ms0216/hhkb-split/docs/hardware/provisional-values.md

# まだ実測していない値

**推定で埋めた値と、確かめた値が区別できないと、どこがまだ危ないのかが
分からなくなる。** この案件では、タクトスイッチの向きも XIAO のピンピッチも
推定のまま断定し、どちらも利用者に指摘されて初めて誤りだと分かった。

ここは `[暫定]` と書かれた定数の一覧。
[tools/test_constants.py](../../tools/test_constants.py) が
**コードとこの表がずれたら落ちる**ようにしてある。書き漏らしも、
実測して確定したのに残っている行も、どちらも検出される。

---

## 一覧

| 定数 | 現在値 | 何の値か | どうやって確かめるか | 外したときの影響 |
|---|---|---|---|---|
| `CAP_LIFT` | 6.2mm | プレート上面からキーキャップ底面まで（MX ＋ キャップ） | MX スイッチとキーキャップが届いたら測る | **全段のキートップ高さが実機とずれる。** ここから `PLATE_TOP_FRONT` を逆算しているので影響は全体に及ぶ |
| `CAP_H_HOME` | 7.6mm | ホーム段のキーキャップ自体の高さ | 同上 | 同上 |
| `CAP_H_QWERTY` | 9.16mm | **QWERTY 段**のキャップ高さ。上 2 段だけ背の高いものを混ぜる決定（open-gaps #21）による | **実機のキートップ 35.6mm に一致させるのに要る高さを逆算した要求値で、製品の実測ではない。**この高さの MX 用キャップを実際に探し、買ってノギスで測る | 実機のキートップ高さとずれる。`test_our_design_actually_reaches_the_real_keytop_heights` が差を表に出す |
| `CAP_H_NUMBER` | 11.12mm | 同・**数字段** | 同上（実機 40.0mm から逆算） | 同上 |
| `SOCKET_DROP` | 3.2mm | Kailh ホットスワップソケットが基板下へ出る量 | ソケットが届いたらノギスで測る。**データシート（PG151101S11: 板下 1.80）と kiswitch モデル（端子込み 2.01）とは突き合わせ済み**で、3.2 は 1.19mm 保守側（`test_the_socket_box_contains_the_third_party_model`） | 大きすぎればケースが無駄に厚い。小さすぎればソケットがケース床に当たる |
| `PLATE_TO_PCB` | 3.5mm | プレート下面から基板上面までの距離 | MX スイッチが届いたら、プレートに挿して測る | **キートップの高さが実機とずれる。** HHKB 再現の根幹 |
| `BATT_BOX_W` | 16.6mm | 同・短辺（前後） | 同上 | コブの奥行が足りなくなる。ケースの作り直し |
| `BATT_BOX_H` | 16.8mm | 同・高さ | 同上 | 電池室の高さが足りず、傾いた基板を突き上げる |
| `ANTENNA_L` | 3.5mm | XIAO のチップアンテナが占める長さ（USB と反対の端から） | XIAO の実物か、Seeed の基板図で測る。**いまは概数** | アンテナが本体基板の下から出ているかの判定がずれる（open-gaps #23） |
| LED の点灯電流 | **1〜2mA（推定）** | XIAO 基板上の RGB LED 1 色ぶん（直列抵抗込み）。**コードの定数ではない**ので `tools/` の検査対象には無い | 実機で点灯／消灯の差をシャントで測る（Task C4/C5）。**未実測** | **接続中は消灯なので定常状態では効かない**（実機もそうなっている）。効くのは**未接続で放置したとき**で、緑／青の点滅は 50% デューティ。待機 20µA に対し 3 桁大きいので、長く未接続のまま置くと電池を食う。大きければデューティを下げる（open-gaps #43） |
| `USB_SHELL_EXPOSED` | 1.0mm | 完全に挿さった状態で、プラグの樹脂とケース表面の間に**見えている金属の長さ** | 実機に挿して測った（2026-08-09・ケーブル 1 本）。**ケーブルによって違う**ので、手持ちの数本で測り直し、いちばん短いものに合わせる | 短いケーブルが**奥まで挿さらない**（open-gaps #28） |
| `ANTENNA_W` | 3.5mm | XIAO のチップアンテナの幅 | 現物を実測（概数）。**長手の向きが未確定**なので大きいほうを両方に使っている | 子基板の配線をアンテナの真下から外せるかの判定がずれる |
| `USB_PLUG_W` | 12.0mm | **利用者が挿す USB-C ケーブルの、オス側プラグの樹脂の胴体**の幅 | 手持ちのケーブル数本を測った最大値（分解能 1mm の器具・2026-08-09）。**ノギスで測り直す**。買い足したケーブルが太ければ入らなくなる | 奥の壁の穴が小さすぎて、**ケーブルが挿さらない**（open-gaps #28） |
| `USB_PLUG_H` | 7.0mm | 同・厚さ | 同上 | 同上 |
| `SW_PWR_W` | 3.9mm | 電源スイッチ本体の幅（背面パネルに沿った左右）。**SS12D01G4-G で確定**（2026-08-12） | データシート（SWITRONIC V2.3）と秋月の商品ページが一致。**届いたらノギスで確認** | **左半分の空きは 10.6mm しかない。**超えると入らない |
| `SW_PWR_H` | 8.8mm | 同・高さ（上下）＝ 本体の長辺。溝の高さを決める | 同上 | コブの内部 15.5mm を超えると入らない |
| `SW_PWR_BODY_D` | 3.5mm | 同・本体だけの奥行（壁の内面 → 本体の背面）。**奥のリブの位置＝押し込み側の抜け止めがここで決まる** | 同上 | 大きいと本体が奥のリブに当たって座らない。小さいとリブが本体に届かず**押し込むと落ちる** |
| `SW_PWR_LEAD_D` | 5.0mm | 端子が本体の背面から出る長さ | 同上 | 短く見積もると端子がリブに当たる |
| `SW_PWR_WIRE` | 2.5mm | 端子の先にリード線を回すぶんの余裕 | **見積もり。**はんだ付けして実測する | 足りないとリード線がコブの内壁に押される |
| `SW_PWR_KNOB` | 4.0mm | ツマミの突出量（本体の上面から） | 図面 `L 4` ／ 商品ページ「操作部長さ 4mm」。**2 つの出所が一致** | 窪みの底までの壁 1.4mm を貫いて外へ 2.6mm 出る。小さいと**指が掛からない** |
| `SW_PWR_KNOB_W` | 1.5mm | ツマミの断面（1.5 角） | 図面 | スロット幅 2.6mm に対する余裕 |
| `SW_PWR_TRAVEL` | 2.0mm | ツマミのストローク | 図面 | スロット長 5.0mm に収まること |
| `SW_PWR_PIN_W` | 0.5mm | 端子の幅（0.5 × 0.3）。奥のリブのスリット幅を決める | 図面 | 広げすぎるとリブが痩せて抜け止めが弱る |
| `M2_INSERT_L` | 4.0mm | M2 熱圧入インサートの**長さ** | 買う製品を決めて外形から入れる。届いたらノギスで確認 | **子基板のボスは 5.0mm しか掘っていない。**5.7mm を買うと入らない |
| ~~`FFC_LENGTH`~~ | **80mm（2026-08-16 確定）** | 本体基板と子基板をつなぐ FFC の長さ（0.5mm ピッチ 12 芯・**A タイプ**） | ~~実際に買う製品を決めて、その長さを入れる~~ **済み**（uxcell 80mm A タイプ 20 本入り。[open-gaps #19](open-gaps.md)） | 必要 54.0mm（直線 29.0 ＋ `FFC_SLACK`）に対し余り 26mm |
| `FFC_SLACK` | 25mm | 直線距離に足す余裕（垂直の落差・両端の曲げ・抜け止め） | ケースを 1 台組んで、実際の引き回しで測る | 足りないとケーブルが張り、コネクタが抜ける |
| `RUBBER_T` | 2.0mm | ゴム足の厚み。**接地までの高さは（厚み − 座ぐり 0.6mm）**で、チルト脚の 0° の高さと揃える必要がある | 買う製品を決めてノギスで測る | **打鍵面の傾斜がずれる。**0.6mm 違うと 0.41°。傾斜は動かしてはならない値 |
| `SW_BODY_W` | 15.6mm | MX スイッチ上部ハウジングのつばの幅（組み立て検査 #29） | スイッチが届いたらノギスで測る | 隣のキーやベゼルとの余白の判定がずれる |
| `SW_UNDER_W` | 14.0mm | 同・プレート下の下部ハウジングの幅 | 同上 | プレート開口 14.0 との勘合の判定がずれる |
| `CAP_GAP` | 0.65mm | 隣接キーキャップ間の隙間（DSA の公称 18.4mm から逆算） | キャップが届いたら実測。プロファイルを変えたら入れ直す | キャップどうし・ベゼルの縁（余白 1.8mm）と当たる |
| `CAP_WALL` | 1.3mm | キーキャップ側面の肉厚（**中は空洞**。裾がスイッチのステムとスタビの挿子を飲み込む） | キャップが届いたらノギスで測る | 薄すぎると偽の干渉が出る（実物のスタビはプレート上面から 10.5mm 立つ）。厚すぎると、本当に当たる場合を見逃す |
| `CAP_TOP_T` | 1.3mm | 同・天面の肉厚（空洞の深さ ＝ キャップ高さ − これ） | 同上 | 空洞が浅いと、スタビの挿子が天井に当たったことになる |
| `STAB_PAD` | 0mm | スタビの予約の余白。**寸法本体は記録（kiswitch モデルのハウジング bbox 6.8×19.2）から取る**。旧 `STAB_BODY_D` 7.0 はモデルの前後 19.2 より小さく、予約が実物を覆っていなかった（2026-08-11 発覚） | スタビが届いたらノギスで測り、モデルより大きい差をここに入れる | プレート下の空間の取り合いの判定がずれる |
| `USB_MATE_DEPTH` | 6.0mm | 完全に挿さったとき金属シェルがメスに入る深さ | 実機とケーブルで挿し込み量を測る | プラグを置く位置がずれ、#28 の再発検査が甘くなる |
| `USB_PLUG_SHELL_T` | 0.3mm | プラグの金属シェルの肉厚（**中はメスの舌が入る空洞**） | 手持ちのケーブルをノギスで測る | 厚すぎると舌（実物 6.70x0.75）を飲み込んで偽の干渉が出る。薄すぎると、本当に当たる場合を見逃す |
| `USB_PLUG_BODY_L` | 10.0mm | プラグの樹脂の胴体の長さ（検査で効くのは前面の位置だけ） | 手持ちのケーブルを測る | ほぼ無し（後方は空間） |
| `FFC_RIBBON_W` | 7.0mm | FFC リボンの占有幅（12 芯 0.5mm ピッチ 6.0 ＋ 振れ） | 買う FFC の実幅＋経路を組んで測る | 経路の取り合い（子基板ボスとの間など）の判定がずれる |
| `SCREW_HEAD_D` | 3.8mm | M2 なべネジの頭の直径 | 買う品を決めて実測 | 座ぐり・キャップ下の余白の判定がずれる |
| `SCREW_HEAD_H` | 1.6mm | 同・頭の高さ | 同上 | 同上 |
| `SCREW_L_MAIN` | 14.0mm | 上シェルの手前の取付ネジの長さ。**裏から**（2026-09-06）: 底の座ぐり → 床 → ボス柱 → プレートの切り欠き → 上シェルのベゼル手前バーのインサート | 幾何から選んだ（頭の座 1.8 ＋ インサートの座 11.3〜11.7 ＋ 噛み合い 4.0）。買う前に組図で確認 | 短いと掛からず、長いとバーの上面を突き破る（下穴の上端 16.6、上面 17.8） |
| `SCREW_L_DB` | 5.0mm | 子基板の取付ネジの長さ | 同上 | 同上 |
| `DB_SOCKET_SEAT` | 8.5mm | 普通のメスピンソケットの座高。**プロトタイプ期だけ挟む**（open-gaps #27・2026-08-12 に利用者が承知で決定）。ここから `DB_XIAO_LIFT` 10.5 ＝ 座高＋ヘッダ樹脂 2.0 と `DB_STACK_H` 15.0 が導かれる | **買ってノギスで測る。**分解しての足し算ではなく、**挿した状態で「子基板の上面から XIAO の基板下面まで」**を直接測る（受けが 5.5mm より浅いとピンが底突きして足し算より高くなる） | **背面 USB-C の穴の高さがずれ、ケーブルが挿さらない**（#28 の再来）。ケースの再生成で追随する。**アンテナは既に 0.72mm で承知済み**なので、ここが増えてもさらに悪くなるだけ |
| `SCREW_L_PCB` | 5.0mm | 本体基板をプレート裏の柱へ締める M2 の長さ（open-gaps #36） | **買う前に組図で確認。**板 1.6 を貫いて柱へ 3.4mm 噛む。頭は φ≦3.8・高さ≦1.6 （基板の裏に出るので、ソケットの 3.2mm より低いこと） | 短いと噛まない。長いと柱を突き抜けてプレート表面に出る |
| `SKIRT_FIT` | 0mm | 上シェルのスカートの内面と下シェルの側壁の帯の外面の隙間（案 A・2026-09-05） | **0 ＝ 接触**は利用者の判断（隙間はガタになる。合わなければ帯を削る）。クーポン（#11）で壁の位置ずれを測ってから 0 か 0.1 か決める | 太い個体は被さらない（帯をやすりで削る）。大きくすると横に遊びが出て合わせ目がずれる |
| `BATT_GUIDE_X1_FROM_END` | 14mm | 電池ボックスの裏面のケーブル受けの突起 1 の位置（黒線側の端から）。仕切り壁をそこだけ切り下げる | **利用者が現物を実測**（2026-09-06）。目測寄り | 位置がずれると突起が仕切り壁に当たり、箱が締められない |
| `BATT_GUIDE_X2_FROM_END` | 53.5mm | 同・突起 2 | 同上 | 同上 |
| `BATT_GUIDE_X3_FROM_END` | 93mm | 同・突起 3 | 同上 | 同上 |
| `BATT_GUIDE_W` | 4mm | 同・突起の幅（切り欠きは +2） | 同上 | 同上 |
| `BATT_GUIDE_H` | 5.5mm | 同・突起の高さ（床からこの高さまで壁を残す） | 同上 | 高すぎると当たる。低すぎると壁が箱を受けない |
| `BATT_HOLE_Z_LEFT` | 5.0mm | 電池ボックスの取付穴の、床（箱が接する面）から穴の中心までの高さ（左） | **利用者が現物を実測**（2026-09-06）。左右で箱の上下が逆で穴は中心から外れている | 仕切り壁のボスの高さが穴に合わず、締められない |
| `BATT_HOLE_Z_RIGHT` | 11.5mm | 同（右） | 同上 | 同上 |
| `BATT_HOLE_X1_FROM_END` | 75.9mm | 電池ボックスの取付穴 1 の、黒線側の端からの位置 | 図面 3251A-0410 の 75.9±0.5。**どちらの端が黒線側かは現物で確認** | 仕切り壁のボスの x がずれ、締められない |
| `BATT_HOLE_X2_FROM_END` | 82.8mm | 同・穴 2 | 図面の 75.9 に隣の 6.9±0.2 を足した。同上 | 同上 |
| `FOOT_PEG_H` | 2.4mm | チルト脚の差し込みピンの長さ。**4.0 から短縮**（ピン受けボスが J_MAIN コネクタに食い込むため。open-gaps #29） | **印刷して、φ4×2.4mm で脚が保持できるか確かめる**。緩ければ径や勘合を調整 | 脚が抜ける・がたつく。傾斜の信頼性を失う |
| 3V3 の往復ループインダクタンス | **約 145nH（推定）** | XIAO の 3V3_OUT → FFC → 主基板の 595（C_U1）までの直列 L。**コードの定数ではない**ので `tools/` の検査対象には無い。内訳は子基板トレース 24nH ＋ FFC 80mm 64nH ＋ 主基板トレース 57nH（[decisions/2026-08-16-ffc-loop-inductance.md](decisions/2026-08-16-ffc-loop-inductance.md)） | **机上の計算のみ。実測していない。**確定には LCR/TDR が要る。単位長の値は Würth の 0.5mm ピッチ FFC の公表値（Z₀=130Ω・62pF/m）と平行 2 導体の解析式の 2 系統から出し、0.6〜1.05nH/mm で一致した。**uxcell 品そのものの Z₀/C は公表が無い** | **C_DB 削除の判断には影響しなかった**（595 のエッジは直近の C_U1 が 58:1 で取るため。**削除は 2026-08-16 に実施済み**・open-gaps #45）。幅を全部悪い側に振っても約 190nH で分流比 45:1。**桁が 1 つ違っていた場合に効くのは、将来 FFC 越しに速い信号を増やしたとき** |
| `XIAO_LED_DX` / `XIAO_LED_DY` | +5.71 / +15.83mm | LED の窓（#43）の中心。子基板中心 → XIAO の RGB/充電 LED 群の中心 | **Seeed 公式 STEP モデルの読み取り**（pcb_parts.json の 4 パッド群）。**実物の XIAO を点灯させ、窓（φ5）から見えることを確認して確定**。向きの取り違え（鏡像）の型に注意 | 窓から LED が見えない。ケースの刷り直しで済む（基板に影響しない） |
| `SCHOTTKY_VF` | 0.4V | B5819W（C8598）の順方向電圧降下。**実使用の 1〜3mA での値**（2026-08-09 に実測した接続待機は 0.66mA で、想定していた 10〜15mA より 1 桁小さい） | **電流計を直列に入れて電流を確定させ**、そのうえでダイオードの両端を測る。**10Ω シャントの両端を電圧で読む方法は成立しない**（ブレッドボードの接触抵抗が10Ω に対して大きすぎる。2026-08-09 に実測で判明）。1N5819 で 0.23V という値を一度出したが、その方法で測ったので**破棄した** | **維持側の下限（レール＋Vf）の見積もり**が決まる。打ち止めは #34 の決定で `max(維持, 起動)` になったので、**実測して下げても打ち止めは起動の限界 2.40V より下がらない**（下げすぎてブラウンアウトする経路は式で塞いだ）。基板には影響しないので発注はせき止めない |

---

## ✅ `BATT_ESR_END` は実測で埋まった（2026-08-11）

**使い古しのアルカリ 2 組で測った。**100Ω × 4 本を並列にした **25.0Ω** を
負荷にし、開放電圧と負荷時の電圧の差から求めた（基板は使っていない）。

| 電池 | 開放 → 負荷時 | 電流 | **内部抵抗（2 本ぶん）** |
|---|---|---|---|
| 1.34V/本 **Panasonic EVOLTA NEO LR6(INJ)** | 2.69 → 2.43V | 97mA | **2.68Ω** |
| 1.07V/本 **三菱電機 LR6(N)** | 2.16 → 1.58V | 63mA | **9.18Ω** |

**採ったのは 9.18Ω。**打ち止めは 1.20V/本 なので、**1.07V/本 は製品が到達する
前に止まっている領域**＝本番で経験する内部抵抗は必ずこれより小さい。**保守側。**

**補間しなかった。**1.20V/本 の値は線形補間 6.05Ω・対数補間 5.07Ω と、
**形の仮定で 1Ω 動く。**測った点をそのまま使うほうが推論が 1 つ減る。

> **⚠️ 想定の 6 倍あった**（1.5Ω → 9.2Ω）。**それでも合格する**が、
> 合格の理由が変わったので `test_the_margin_covers_the_transmit_droop` の
> 比較相手も直した（100mV → **打ち止めのレール 2.00V とマイコンの下限
> 1.70V の差＝300mV**）。ソケットが律速なので、打ち止めではマイコンに
> 300mV の余裕がある。

**⚠️ 銘柄と温度で変わる。**アルカリとマンガンで 5 倍、冷えると増える。
**だからここは典型値ではなく「悪い側の境界」を置いている。**

## ✅ 電池の保持は「一直線型の電池ボックス」に決まった（2026-08-11・利用者）

**買う品**: **BH-325-1A150**（Comfortable Electronic 製・秋月電子 110201・¥60）
「電池ボックス 単3×2本 リード線・**たて一列**」。外形 **109 × 16.6 × 16.8mm**。

裸の電池を電極バネで保持する案と比べ、**組み立てと公差が 3D プリントの
精度に依存しない**のが決め手（`CLEARANCE` は未実測 / open-gaps #11）。

**長辺が 109mm ちょうど**で、裸の電池 2 本＋電極の占有と同じだった。
左右方向に広がらないので、**背面の電源スイッチの窓（左 10.56mm）が無傷**。
広がる場合そこが最初に潰れるので、`gen_case.power_switch_x_center` が
窓を測って落とすようにしてある。

### 何を取り違えていたか（記録として残す）

この表は以前 `AA_TERMINAL`（＝**電極バネ**の余裕）について
「**電池ボックス**が届いたら測る」と書いていた。**定義と測定対象が
食い違っていた。**その結果、買い物リストに「電池ボックス 単3×2」とだけ
書き、**設計に入らない横並び型（58 × 32mm）を買う**ことになった。

**横並び型はいまも入らない**（コブを 17mm 深くすることになり、ケース奥行が
125 → 142mm。実機 120mm から +22mm）。ブレッドボードでの Task C4/C5 には
そのまま使える。

---

## 確定させる順番

1. ~~**`XIAO_L/W/H`**~~ — **2026-08-08 実測して確定**（21 × 18 × 3mm、
   USB 込みで 4.5mm）。`DB_STACK_H` は **`DB_XIAO_LIFT`（＝ソケットの座高
   ＋ヘッダの樹脂 2.0mm）から導く式**になった（2026-08-12・#27）。
   **残る暫定は `DB_SOCKET_SEAT` 8.5mm 1 つ**（プロトタイプ期のソケット）
2. **`BATT_BOX_W/H`** — 電池ボックス（BH-325-1A150）。L は 2026-09-06 に実測 109.0 で確定済み。W/H はまだ。
   いまは通販の商品ページの記載値（下記）
3. **`SOCKET_DROP`** — ソケット到着後
4. **`PLATE_TO_PCB`** — MX スイッチとキーキャップ到着後。
   ここが決まると `PLATE_TOP_FRONT` を動かしてホーム段 31.6mm に合わせられる

---

## 確定させたときの手順

1. 実測値を `tools/envelopes.py` に入れ、タグを `[暫定]` → `[確定]` に変える
2. **この表から行を消す**（消し忘れると `test_the_provisional_list_has_no_stale_entries`
   が落ちる）
3. 根拠（測り方と測定値）を [dimensions.md](dimensions.md) に書く
4. `pytest tools` と `python3 tools/gen_assembly.py` を通す
