ms0216/hhkb-split/docs/hardware/pcb-routing-handover.md

# 基板の配線 — 現状と経緯

> **2026-08-28 夜:** J_DB（本体の FFC コネクタ）の口を**奥向き**に回した（open-gaps #19 再開）。ピン表は J_MAIN の鏡像（13−n）。左はパッド座標を保って配線無傷・DRC 0。右も 2026-08-30 に利用者が引き直し、**3 基板とも DRC 0**。同日午後に右 J_DB を 1.63mm 手前へ動かし #19 は決着（残りは左 SCK の露出のみ・任意）。`pcb/matrix_only/` を編集 → `export_matrix_routing → gen_pcb → finalize_pcb → drc → pcb_parts --write/--write-groups`。

## ✅ 2026-08-13 — 回路レビュー 8 件、対応完了

熟練エンジニアの指摘 8 件（回路図・2 層化・GND ベタ・GND ビア・
スティッチングビア・パスコン配置・バルクコン検証・電源ライン太さ）を
すべて反映済み（コミット履歴・[open-gaps #37](open-gaps.md) 参照）。
その過程で **74LVC595（左 U1・右 U1/U2）と D_PWR にネットが 1 本も
付いていない**という致命的欠陥が見つかり、直した。

> **「DRC 0・未配線 0」は、回路が正しいことの根拠にならない。**
> ネットの付いていないパッドは、繋ぐ相手が居ないので**「未配線」に
> 数えられない」**。この欠陥に対して DRC も未配線カウントも完全に無力だった。

回路図（`tools/gen_sch.py`）と ERC、そして**回路図と基板の netlist を
突き合わせる検査**（`tools/test_schematic.py`）を導入して塞いだ。
**発注前の正しい順序は「回路図 → ERC → アートワーク → DRC」。**

**この文書の下は、2026-08-08 頃（手書きルータ → Freerouting 移行時、
基板がまだ 4 層だった時期）に書かれたまま、2026-08-12 の 2 層化
（指摘 2/3）を経て更新されていなかった。**`In1.Cu`（GND 専用の内層）
への言及は、2 層化後は「両面（F.Cu・B.Cu）の GND ベタ」に読み替える
こと。数値（違反件数・ビア数・配線総長）は 4 層時代の実測のままなので、
**2 層化後の値ではない。**最新の値は `pcb/drc_left.json` /
`pcb/drc_right.json` と、この節の上にある「いまの状態」の表を見ること。

## いまの状態

| | 違反 | 未配線 |
|---|---|---|
| 本体基板 左 | **0** ✅ | **0** ✅ |
| 本体基板 右 | **0** ✅ | **0** ✅ |
| 子基板 | **0** ✅ | **0** ✅ |

`tools/test_pcb.py` の `WIP_BOARDS` は空。DRC の検査が skip ではなく
PASS で通っている。

> ⚠️ **2026-08-23 から配線は凍結され、Freerouting は使わない。**
> 利用者が `pcb/matrix_only/` を直接編集し、道具は**写すだけ**
> （利用者「私が PCB を編集するので、それに追従してください」）。
> 現行の手順は CLAUDE.md のコマンド表と同じ:

```
KPY=/Applications/KiCad/KiCad.app/Contents/Frameworks/Python.framework/Versions/3.9/bin/python3.9
"$KPY" tools/export_matrix_routing.py  # 利用者の板 → pcb/matrix_routing.json に写す
"$KPY" tools/gen_pcb.py                # 記録から板を再現できることを確かめる
"$KPY" tools/finalize_pcb.py           # matrix_only ＋ GND ビア → 本番 pcb/
.venv/bin/python3 tools/drc.py         # 確かめる（記録も更新）
.venv/bin/pytest tools -q              # 全検査
```

（以下の Freerouting の記述と `autoroute.py` は**経緯の記録**。
Java と jar の準備もいまは不要。）

---

## 役割分担（2026-08-23 以降）

```
pcb/matrix_only/                  利用者が直接編集する、配線確定済みの板
      ↓  tools/export_matrix_routing.py（写す）
pcb/matrix_routing.json           配線の記録（gen_pcb が再現に使う）
      ↓  tools/finalize_pcb.py（GND ビア fence→ring→stitch→islands を追加）
pcb/hhkb_split_{half}.kicad_pcb   本番。続けて pcb_parts.py --write /
                                  --write-groups / drc.py で記録を更新
```

### 役割分担（旧・Freerouting 期の記録）

```
tools/gen_pcb.py     配置・ネット・ゾーン・設計規則（配線は持たない）
      ↓  pcb/unrouted/hhkb_split_{half}.kicad_pcb
tools/autoroute.py   DSN → Freerouting → SES → ゾーン塗り直し
      ↓  pcb/hhkb_split_{half}.kicad_pcb
tools/drc.py         ハッシュつきで記録
```

例外は**決まりきった局所配線**の 2 つだけ。どちらも経路に選択の余地が無く、
自動配線器に任せると却って悪くなる。DSN からはネットごと外し、配線材は
`(type protect)` で「避けるべき障害物」として渡す。

| | |
|---|---|
| スイッチ → ダイオード | `gen_pcb.prewire_switch_diode`。裏面の L 字 2 本。ビア 0 |
| GND のパッド → ベタ | `tools/gnd_fanout.py`。パッドの長軸方向へビア 1 個 |

---

## 手書きルータをやめた理由

**「残りは引き回しの微調整」という診断が誤っていた。**

- `ROW4` と `ROW1` のような**任意のネット対**が短絡していた。これは経路の
  良し悪しではなく、**自分が引いた線を見ていない**ことの帰結。衝突判定を
  持つルータは構造的に出せない
- リップアップも大域的なコスト関数も無いので収束しない。25→34、24→144、
  23→36 と何度も戻した
- `SOIC-16` はコートヤード 10.49mm で、帯 9.25mm に**そもそも入らなかった**。
  位置の微調整（`-1.8`）は、どちら側にはみ出すかを選んでいただけ

設計: [2026-08-08-pcb-autoroute-design.md](../superpowers/specs/2026-08-08-pcb-autoroute-design.md)

---

## Freerouting を通すために要った 3 つ（全部つまずいた）

### 1. `J_DB`（FFC）がダイオード列に載っていた

上段キーのダイオードは帯へ **1.75mm 食い込み、19.05mm ピッチ**で並ぶ。
帯の部品で `J_DB` だけ背が高く（7.9mm）、その x がちょうど `D3` の列だった。
短絡・コートヤード重なり・`ROW0` の未配線は**全部これ**。

→ `J_DB` とその玉突きで `C_BULK` / `C_MCU`（のち `C_RAIL` に改名。
**2026-08-14 に削除。open-gaps #40**） をダイオードの隙間へ移した。

**帯に部品を足すときは、ダイオード列の x を避けること。**

### 2. GND パッドがベタに届かない

GND ベタは `In1.Cu` の 1 層だけ、GND パッドは全部 `B.Cu` の SMD。
間のビアを Freerouting 任せにすると、混んだ区画で失敗する
（対応する SMD ピンの **42% しかファンアウトできなかった**）。

→ `tools/gnd_fanout.py` が配置段階に決定的に立てる。向きは**パッドの長軸**
（支配軸でやると FFC の横並びパッドで隣に刺さる。実際にやった）。

**`ImportSpecctraSES` は既存の配線を全部作り直すので、取り込みのたびに
自分で引いたものが消える**（実測: GND のビア 7 個 → 0 個）。
`autoroute.py` が上の 2 つとも立て直す。

### 3. DSN に GND を残すと Freerouting が NPE で落ちる

ピンだけ消してネット定義を残す、のような中途半端なやり方をすると
`NullPointerException` で GUI ごと落ちる。ネット定義・クラスの一覧・
plane 宣言を**まとめて**消すこと（`_strip_prewired`）。

ファンアウトの配線材は `(type protect)` に変えて、ネットを持たない
固定障害物として渡す。**消すと避けてくれない。**

---

## 取付穴（2026-08-12 に足した。**配線の制約が 1 つ増えた**）

**本体基板に取付穴がある**（左 6・右 8・φ2.2 / M2）。open-gaps #36。
それまで本体基板には**固定具が 1 つも無く**、保持はスイッチ 54 本のピンの
摩擦だけだった（スイッチを抜くとソケットのはんだに剥離力がかかる）。
プレートの裏から柱が降りてきて、基板を下から M2 で締める。

位置は `tools/interface.py` の `PCB_MOUNT_POSITIONS`。**手で決めない。**
次の 4 つを**同時に**満たす場所しか使えない:

| 条件 | 何で見ているか |
|---|---|
| 基板の縁から 1.0mm 内側 | `test_the_pcb_is_actually_fastened_to_the_plate` |
| **キーとプレート開口**に当たらない | 同上（`find_mounts.keepout_boxes`） |
| **実装部品**に当たらない | 同上（`pcb_parts.json` の bbox） |
| **コートヤード**に当たらない | DRC（`Courtyards overlap`） |
| **配線に当たらない**（2026-08-22 に足した 5 つ目） | 下の節 |

⚠️ **この 4 つを別々に確かめて 3 往復した**（2026-08-12）。コートヤードだけ
見て置いたらキーに当たり、キーを避けたらコートヤードに当たった。
**穴を動かしたら `gen_pcb → autoroute → drc` をやり直すこと。**

⚠️ **配線が通らないからといって穴を減らさないこと**（利用者の指示）。
位置を工夫する。現に左 6・右 8 のまま DRC 0 で通っている。

### 2026-08-22 に右の H0 と H2 を動かした（**5 つ目の条件が増えた**）

**穴を決めたときの目的関数に「配線」が入っていなかった。**当時は
「キーから最寄りの留め点までの最大距離を小さくする」の 1 本だけで、
**横ライン（COL → U1/U2）はまだ存在しなかった。**あとから引いた線が
穴にぶつかり、利用者に「非常に邪魔」と言われて初めて分かった。

| | 前 | 後 | 配線までの隙間 |
|---|---|---|---|
| **H0** | (0.00, 10.00) | **(0.00, 28.00)** | 0.675 → **1.607mm** |
| **H2** | (-77.00, 26.50) | **(-82.40, 26.50)** | 0.460 → **2.540mm** |

**H0 は横ラインの帯（板 y=86.2〜92.9）の真ん中に立っていた。**
移動先は第 0 行と第 1 行のキーの隙間で、**H7(-38)・H6(38)・H3(81) と
同じ y=28 に載り、x は -38 / 0 / 38 が 38mm 等間隔になる**
（それまで H0 は他のどの穴とも x も y も揃っていなかった）。

**H2 は ROW0 の縦降りを挟んでいた。**⚠️ **ROW0 は `ROW_A` ではなく
`ROW_C`**（D1 が繋がっている先で確かめる。名前と行番号は一致しない）。

⚠️ **H2 では「縁までの余裕」と「配線までの隙間」が真正面から競合する**
（`ROW_C` の F.Cu 縦降りが板 x=71.34 にいる）。一度 x=-84.65 まで
逃がして配線 4.79mm を得たが、利用者「基板端すぎる」。**縁 3.40mm を
取って配線 2.54mm で折り合わせた。**x=-79.90 まで戻すと配線 0.04mm で落ちる。

**どちらもキーからの最大距離 35.33mm を悪化させていない**（動かす前と同じ）。
DRC も動かす前と同じ（エラーは `annular_width` 1 件で、これは
利用者が引いた `V3V3` のビアが外径 0.5 / 穴 0.3 で、穴の件とは無関係）。

#### この移動で 1 件出た課題: **名札がキーの枠に重なっていた**

H0 を動かしたら `silk_overlap` が 1 件増えた。追ったら、**取付穴の名札は
フットプリントの既定で穴の 3.15mm 手前（-Y）に出る**が、そこはたいてい
**すぐ手前のキーのシルクの枠の中**だった。

**増えたのは 1 件だが、同じものが前から 4 件出ていた**（右 H1/H3/H6/H7）。
`silk_overlap` は警告なので誰も見ていなかった。**動かしたことで 5 件目が
生まれ、それで初めて 4 件に気づいた。**

→ `gen_pcb._place_hole_label` が**手前・奥・左・右を試して、キーの枠に
当たらない向きへ名札を回す。**全部当たるなら既定のまま置く
（**名札を消して黙らせない**——消すと基板上で穴が識別できない）。

    silk_overlap  右 13 → 9 件 ／ 左 7 → 3 件（取付穴がらみは 0）
    増えた違反は 0 件（前後を突き合わせて確認）

⚠️ **故意に壊して確かめた。**逃がし先を既定の 1 方向だけにすると
**DRC が 5 件出す。**通ったから正しい、ではない。

⚠️ **比較のとき `kicad-cli` に基板だけ渡さないこと。**重大度は
**隣のプロジェクトファイル**から読むので、`/tmp` に基板だけ置いて
DRC を回すと既定値で走り、`hole_to_hole` 34 件が消えて
`copper_edge_clearance` 2 件が現れる。**別の板に見える。**

---

## 機械で守っていること

| 検査 | 守るもの |
|---|---|
| `test_the_main_board_is_two_layers_with_ground_poured_on_both` | 層構成が F.Cu・B.Cu の 2 層で、**両面とも** GND ベタが実際に塗られていること（2026-08-12 の 2 層化で `test_the_ground_plane_is_not_cut_by_routing`〈`In1.Cu` に配線 0 本〉から置き換わった） |
| `test_every_ground_pad_reaches_the_plane` | GND パッドの脇にビア。外すと未配線が左 6・右 7 件 |
| `test_there_are_enough_ground_vias_to_tie_the_two_planes` | GND ビアが下限（`MIN_GND_VIAS`）以上あること（指摘 4） |
| `test_few_pieces_of_ground_copper_are_left_floating` | 浮いた GND の区画が増えていないこと（指摘 5 の番人。必達は 0 個） |
| `test_the_electronics_do_not_bite_the_key_sockets` | **電子部品がキーのソケットに当たっていないこと。**走査の正解は `circuit.py` の宣言から導く。⚠️ **2026-08-23 に「帯 9.25mm の内側か」から変えた**——帯は手段で、目的は「当たらないこと」。利用者が U2 を帯の外へ移したら、**何にも当たっていないのに赤が出た** |
| `test_the_board_declares_the_netclass_used_for_routing` | **自動配線器はネットクラスしか見ない。**既定値頼みにしない |
| `test_the_routing_was_made_from_the_current_placement` | 配置を変えたのに配線し直していない状態 |
| `test_the_ffc_cable_reaches_the_daughterboard` | FFC が子基板まで届くこと。**部品を動かすと黙って届かなくなる** |
| `test_both_halves_can_use_the_same_ffc_cable` | 左右で同じケーブルが使えること（部品表を 2 種類にしない） |

いずれも**故意に壊して落ちることを確認してから**足した。

---

## 配線の質（手書き → Freerouting）

⚠️ **この表は 2026-08-08 頃、基板がまだ 4 層だった時期の実測。**
2 層化・GND ビア増量（指摘 4/5）後の値ではない。**現在のビア数は
GND だけで左 732 個・右 913 個**（84df0cb・86e0101 の実測）で、
この表の数値とは前提が違う。層構成の推移を示す歴史的記録として残す。

| | 左 | 右 |
|---|---|---|
| DRC 違反 | 33 → **0** | 32 → **0** |
| 総長 | 1817 → **1538mm** | 2290 → **1902mm** |
| ビア | 58 → **40** | 68 → **51** |
| 遠回りの最大 | 2.3 → **1.6** | 2.3 → **1.6** |
| `In1.Cu` の配線 | 0 → 0 | 0 → 0 |
| GND の島 | 1 → 1 | 1 → 1 |

**ビアは手書きより減った。**一度は左 68・右 111 まで増えたが、原因は
`SW*_D`（スイッチ → ダイオード）だった。数 mm の接続のために自動配線器が
内層へ往復し、左 30 個・右 62 個をそこに使っていた。**この配線は経路に
選択の余地が無い**ので `prewire_switch_diode` で自分で引き、DSN から
外した。左右の比（51/40 = 1.28）がキー数の比（34/27 = 1.26）とほぼ
一致し、非対称は規模差だけで説明がつくようになった。

**`F.Cu` は 0 本。**信号は `In2.Cu` と `B.Cu` で足りている。

**この実測が、2026-08-12 の 2 層化の根拠になった**
（[decisions/2026-08-07-four-layer.md](decisions/2026-08-07-four-layer.md)）。
当時は「4 層をやめられるという意味ではない」と判断していたが、
これは誤りだった。信号が 2 層に収まっている以上、`In1.Cu`（GND 専用の
内層）を残す理由は無く、実際にその後 2 層へ確定した。GND ベタは
両面（F.Cu・B.Cu）で受ける形に変わっている。

---

## 配線の思想（B.Cu が主・F.Cu は橋）

**2026-08-15・利用者の指摘**「可能な限り B.Cu で配線し、交差するところだけ
ビアで最短だけ F.Cu に潜ってすり抜ける、という形になっているはずだが、
守られていない箇所が至る所にある」。

**実測したら本当だった。** F.Cu の連結成分ごとに長さを測ると、
「短い橋」ではなく**端から端まで F.Cu を走る本線**が並んでいた
（左 COL0 が 78mm、右 CS が 84mm、右 V3V3 が 93mm）。
両端ビア間の直線距離との比（detour）が 1.0 前後、つまり
**迂回している橋ではなく、F.Cu に移住した本線**。

→ `autoroute.py` の `_autoroute_settings` が DSN にコストを入れる。

| | F.Cu | 成分数 | ≤5mm の橋 | >10mm | ビア |
|---|---|---|---|---|---|
| 左 前 | 531mm (22.3%) | 19 | 6 | 12 | 1028 |
| 左 後 | **245mm (10.5%)** | 35 | **22** | **7** | 1008 |
| 右 前 | 804mm (25.1%) | 28 | 8 | 19 | 1281 |
| 右 後 | **391mm (12.3%)** | 49 | **29** | **10** | 1269 |

**F.Cu の銅が半分以下になり、本数は増えた**——長い本線が短い橋に
置き換わったということ。**ビアはむしろ減っている**（左 1028 → 1008）。
DRC は 3 枚とも**違反 0・未配線 0**。

### 効くのは `via_costs`。層のコストではない

層コスト比を 5 / 20 / 100 と振っても F.Cu は 22.1% で**全く動かない**。
動くのは `via_costs`——**B.Cu に留まるにはビアを惜しまず打つ必要がある**
ので、ビアが高いと長い F.Cu の迂回を選ぶ。

### ⚠️ `via_costs` を 0 にしてはいけない（F.Cu が増える）

2026-08-15・利用者の問い「ビアコストは 0 とか可能な限り最小にできないのか」。
**実測したら逆効果だった。**

| via_costs | 左 F.Cu | 右 F.Cu | 右ビア |
|---|---|---|---|
| 30 | 22.1% | — | — |
| 5 | 15.0% | 19.5% | 90 |
| **2** | **14.6%** | **16.8%** | 103 |
| 0 | 16.8% | **24.8%** | 119 |

0 では右が 24.8%——**何もしない状態（25.1%）へほぼ逆戻り**する。
ビアは 119 個に増えているのに F.Cu も増える、両方損の状態。

**ビアが無料だと「橋を短くする理由」が消えるため。**3 回潜って戻る経路も
1 回で済む経路も同じ値段なので、ルータは経済性を考えるのをやめてふらつく。

> **「短い F.Cu は歓迎、長い F.Cu は嫌う」を実現しているのは、
> ビアにわずかな値段が付いていること。**橋が短いほどビア 2 個分の元が
> 取れるので短い橋が勝ち、長い F.Cu は「そんなに走るなら潜り直せ」と負ける。

なお **Freerouting のコスト関数では「その連結成分の全長」のような大域的な量は
書けない**（`AutorouteSettings` にあるのは via / trace / ripup のみ。
逆アセンブルで確認）。`via_costs` がその代理として働いている。

値は単調ではない（4 → 5 → 6 が行ったり来たりする）。コストを変えると探索
経路ごと変わるため。**1〜2 ポイントの差で良否を決めないこと。**

### クリアランスの余裕を 20 → 30µm に上げた

B.Cu が密になったぶん、Freerouting の丸め不足が顕在化した
（左 0.1992mm・右 0.1967mm ＜ 規則 0.2000mm）。
20µm では違反 左1/右2、30µm で **違反 0/0/0・未配線 0/0/0**。

### ⚠️ 2026-08-14 の「autoroute_settings を足すな」は誤りだった

当時「左が未配線 1 → 66 本に激増、値を変えても同じなので**ブロックの
存在そのものが悪い**」と結論して禁止していた。**そうではない。**

1. **挿入位置が `parser` スコープの中だった。**`"\n  )\n"` を正規表現で
   探すと structure ではなく **parser の閉じ括弧に先に当たる**。
   未知のスコープは黙って捨てられるので、**値を変えても何も起きない。**
   「値ではなくブロックの存在が効く」の正体はこれ
2. **層ごとのコストは `(layer_rule <層名> ...)` の中**にある。当時は
   global の `via_costs` しか書いておらず、**層コストは一度も
   設定されていなかった**

構文は Freerouting 2.3.0 の `io/specctra/parser/AutorouteSettings.class` を
逆アセンブルして確認した（推測ではない）。`_autoroute_settings` は
**入れたあとに括弧を数え直して structure の内側かを検査する**。
故意に parser の中へ入れて、検査が捕まえることを確認済み。

**教訓: 「効かない」と「間違った場所に書いた」は区別がつかない。**
設定を足したら、**効いたかどうかを数字で見る**（CLAUDE.md の作法 5）。

### 途中で見つけた別の欠陥（**まだ直っていない。手を付けていない**）

**`gnd_fanout` のスタブは `B.Cu` 決め打ちで引かれているが、SMD の GND
パッドは左右 11 個とも F.Cu にある。**つまり**スタブはパッドに触れて
いない**（空中から始まってビアに刺さるだけ）。それでも繋がって見えて
いたのは F.Cu のベタがパッドに被っていたからで、**繋いでいたのは
スタブではなくベタだった。**

途中の設定（`via_costs=5` + 余裕 20µm）で B.Cu が密になったとき、
ベタが割れて右の `U1` パッド 13（74LVC595 の GND）が孤立し、露見した。
ビアは 1.54mm 離れた位置にあり、間を繋ぐ銅がどこにも無かった。

**最終的な設定（`via_costs=2` + 余裕 30µm）では顕在化していない**
（違反 0・未配線 0）。**が、直ったわけではない。**ベタの形が変われば
また出る。**潜在的なままなので、いずれ直すこと。**

直そうとして失敗した記録（同じ道を 2 回通らないため）:

| 試したこと | 結果 |
|---|---|
| スタブをパッドの層に合わせる | 右が**違反 0 → 17・未配線 2 → 3** に悪化。F.Cu のスタブが F.Cu の配線と当たる（`_candidates` / `_blocked` はパッドしか見ていない） |
| 同上＋`gen_pcb` から引き直して protect で渡す | 違反 1 まで戻せたが、**孤立が `U1` から `C_U1` へ移っただけ** |
| SMD はパッドの真上にビアを置く | **置けない。**必要な直径 1.7mm に対し TSSOP のパッド幅は 0.4mm・ピッチ 0.65mm。`_blocked` が正しく拒否する |

⚠️ **`spots()` は配線を見てはいけない**という制約がある（配線の前後で
同じ位置を返す必要がある。関数の docstring 参照）。
**素直に直せないのはこのため。**置き場所の探索を層ごとに分けるところから
設計し直す必要がある。

---

## やってはいけないこと（実際に悪化させた）

1. **接頭辞でフットプリントを走査する。**`D`／`SW`／`SW_` で拾うと
   電源部の `D_PWR`／`SW_PWR`／スライドスイッチと、61 個のダイオード・
   スイッチを巻き込む。**同じ事故が 4 回起きている。**
   `re.fullmatch(r"D\d+")` のように絞る
2. **原因を特定せずにパラメータを振る。**必ず
   `kicad-cli pcb drc --format json` で「どのネットとどのネットが、
   どこで」当たっているかを見てから動かす
3. **正規表現でコードを書き換えるとき、置換後を確認しない**

---

## 知っておくとよいこと

- **`.kicad_pcb` のバイト列は保存のたびに変わる。**KiCad が UUID を振り直し、
  フットプリントの書き出し順も変える（同じスクリプト 2 回で 11632 行の差。
  設計は完全に一致）。陳腐化の検出は `tools/boardhash.py` の指紋で行う
- **Freerouting のログの「N violations」は当てにしない。**protect にした
  ファンアウトどうしの接触を数えている。**判定は KiCad の DRC**
- **DRC の件数は実行ごとに数件ゆらぐ**（ゾーンの塗りとの兼ね合い）。
  1〜2 件の差で良否を判断しない

---

## 次にやること

1. ~~ガーバー・BOM・CPL を出す~~（✅ 済み。`tools/export_fab.py` が出す。
   発注前の門 2 つと `tools/test_export_fab_gate.py` 付き）
2. ~~**FFC ケーブルを決める。**~~（✅ **2026-08-16 確定**。uxcell 12 芯
   0.5mm ピッチ **80mm・A タイプ**。`FFC_LENGTH = 80.0`）。届くことは
   `test_the_ffc_cable_reaches_the_daughterboard` が見ている
   （**左右とも 29.0mm** ＋ `FFC_SLACK` 25.0 = 54.0mm 要る。80mm で足りる）。
   **`FFC_SLACK` はまだ暫定**（[provisional-values](provisional-values.md)）

---

## この設計で守られていること（壊さないこと）

- `tools/interface.py` は**凍結境界**。プレート・基板・ケースが共有する
- 検査は「通ること」ではなく「**効いていること**」まで見る。
  故意に壊して検出できることを確かめてから足す
- 実機と違うところは [open-gaps](open-gaps.md) に書く。
  差があること自体は悪くない。**気づけないことが悪い**

## matrix_only を手（スクリプト）で触ったときに落ちる穴（2026-08-31）

スペースキーを 2.75u にするとき、`pcb/matrix_only/` のフットプリントを
KiCad の API で差し替えた。**そのとき 3 回続けて同じ型の失敗をした。**

| やったこと | 何が落ちたか | どう気づいたか |
|---|---|---|
| フットプリント名をテキスト置換 | **名前だけ変わり、パッドは 3u の ±19.05 のまま** | 穴の座標を実測して発覚 |
| API で差し替え | **パッドのネットが全部消えた**（`COL3` / `SW27_D` が無くなった） | 保存後にネットを読んで発覚 |
| 引き直した配線を追加 | **シルクが 0.12mm のまま**（KiCad 標準。JLCPCB の最小は 0.15mm） | `test_the_silkscreen_is_thick_enough_to_print` |
| フットプリントを API で動かした（2026-09-02・#56） | **キー名のシルクは板のテキストなので付いてこない。**古い位置に名札だけ残った（左は穴に掛かって警告 +1、右は警告ゼロで 21mm 離れた名札） | 左は `drc.py` の警告数の差。右は unrouted と matrix_only のテキスト位置を突き合わせて発覚 |

**原因は 1 つ。**`gen_pcb.py` は部品を置いたあとに
**シルクを太らせる・ネットを張る**といった仕上げを一括でやっている。
**matrix_only を直接触ると、その仕上げを通らない。**

→ **matrix_only を触ったら、必ず次を通すこと**（どれか 1 つでも飛ばさない）:

    "$KPY" tools/export_matrix_routing.py   # matrix_only → 記録
    "$KPY" tools/gen_pcb.py                 # 記録 → unrouted（**ここで仕上げが入る**）
    "$KPY" tools/finalize_pcb.py            # → 本番 pcb/
    .venv/bin/python3 tools/pcb_parts.py --write
    .venv/bin/python3 tools/pcb_parts.py --write-groups
    .venv/bin/python3 tools/drc.py

**DRC は 3 つとも見逃した。**シルクの線幅も、ネットの消失も、
パッドの座標も、DRC の 0 件では捕まらない。**検査（pytest）が捕まえた。**
