ms0216/hhkb-split/docs/hardware/electrical-design.md

# 電気設計 — 決定事項と、その根拠

**自分の設計を疑って見直した記録。** 基板を発注すると直せないので、
「動く」だけでなく「使っていて不快でない」水準まで詰める。

---

## 1. 電源

### 1-1. 構成

```
単3×2 ─ スライドスイッチ ─┬─ ショットキー(B5819W) ──┬─ XIAO 3V3
                          │                          ├─ 74LVC595 VCC
                          │                          └─ C2/C3 0.1µF（パスコン）
                          │        （C1 100µF バルクは 2026-08-16 に削除・#44）
                          └─ R1 1MΩ ─┬─ XIAO D0（電池電圧）
                                     └─ R2 1MΩ ─ GND
```

### 1-2. なぜ BAT 端子を使わないか

XIAO の BAT 端子はリポ用充電回路に直結している。**乾電池をつなぐと USB 接続時に
一次電池を充電しようとして液漏れ・破裂の危険がある。** 3V3 ピンへ入れる。

### 1-3. ショットキーが 2 つの役目を兼ねる

| 役目 | 理屈 |
|---|---|
| 電池への充電電流を止める | USB 接続時は 3V3 が 3.3V。電池側 3.0V より高いので逆バイアス |
| USB を挿すと電池を自動で切り離す | 同じ理屈。電池は一切消費されない |

仕様書では P-MOSFET を想定していたが**不要**と判明した。部品が 2 つ減る。

**2026-08-09 に実測で確かめた。**理屈だけで部品を減らしていたのを、
実物で閉じた（[Task C4・C5](task-c4-c5-power.md) の測定 A）。

| | 実測 |
|---|---|
| USB 接続中に電池側へ流れる電流 | **0.8µA。しかも放電の向き**（充電ではない） |
| 対照実験（USB を抜く） | 1.47V ／ 1kΩ = 1.47mA。**測定系は生きている** |

**0.8µA は分圧の 1MΩ×2 が引く 1.53µA から、ショットキーの逆漏れ
0.7µA ほどを差し引いた残り。**アルカリ乾電池に充電電流は流れない。

> **ただし電池 3.00V の 1 点でしか測っていない。**逆漏れは逆バイアス
> （レール 3.3V − 電池）で決まるので、**電池が減るほど増える**。
> 打ち止め付近（2.2V）では符号が反転しうる。C4-3 の掃引で全電圧域を見る。
> 数 µA ならアルカリの自己放電（5.7µA 相当）より小さく危険ではないが、
> **それは測ってから言うこと。**

ショットキーである理由は順方向電圧降下が小さいこと。1N4007（0.7〜1.1V）だと
電池を使い切る前にマイコンの下限を割る。

### 1-3b. 品種の選定（本番基板）

**本番基板は `B5819W`（SOD-123・LCSC C8598・JLCPCB の基本部品）。**
1N5819 の SOD-123 版で、規格（1A・40V・VF 0.6V@1A）は同じ。

| | 定格 | 動作点 | 余裕 |
|---|---|---|---|
| 順電流 | 1A | 10〜15mA（BLE のパルス） | 約 70 倍 |
| 逆耐圧 | 40V | 電池逆挿しで −3V | 13 倍 |

**データシートの数字は、そのままでは動作点の値ではない。**

- **Vf 0.600V は `IF = 1A` での最悪値。**低電流での最大値は規定が無い。
  順方向特性の曲線も **0.1A までしか描かれていない**（25℃ で約 0.28V）。
  実使用の 10〜15mA は図の外なので、**「15mA では 0.2V 前後」とは言えない**
  （以前そう書いていたが、根拠が無かった。2026-08-08 に訂正）。
  設計値は保守的に 0.4V を置き、[Task C4](task-c4-c5-power.md) で実測する

  **ここが効くのは「使い切れる下限」であって、消費電流ではない。**
  直列のダイオードを流れる電荷は負荷と同じで、余計に減るわけではない。
  Vf が高いと打ち止めが上がり（0.4V なら 1.10V/本）、放電曲線の**末尾を
  捨てる**ことになる。0.9V/本まで使う場合に比べて 15〜20% ほど。
  **寿命を決めるのは平均電流（＝ほぼスリープ電流）で、そちらが支配的。**
- **IR 1.0mA は `VR = 40V` での最悪値。**実際の逆バイアスは
  3.3V − 3.0V = **0.3V** しかない。逆方向特性の曲線では 25°C・1V で 4µA
  なので、0.3V ではそれ以下。分圧抵抗が常時流している 1.5µA と同じ桁で、
  アルカリへの充電としては無視できる。**ただし 100°C では 50 倍悪化する**ので、
  [Task C4-2](task-c4-c5-power.md) の実測で確かめる

`B5817W`（20V）は Vf がもう一段低い（1A で 0.450V）が **Extended で
段取り費 $3** がかかる。15mA での差は打ち止めに直すと 0.01V/本 なので、
Basic の `B5819W` を採る（SOD-123 で唯一の Basic）。比較は
[tools/parts.py](../../tools/parts.py)。

**ブレッドボード検証では手持ちの `1N5819`（軸形）を使う。**本番の
`B5819W` と規格が同じ。`SB240LES`（2A）は定格が違い Vf が低く出るので
使わない。

### 1-4. 電池を逆に入れたら

**ショットキーが逆バイアスになり、電流は流れない。** 2 本とも逆なら −3V が
かかるが、逆耐圧 40V なので壊れない。1 本だけ逆なら 0V。
**どちらも安全側に倒れる。**

### 1-5. ~~バルクコンデンサ 100µF~~ → **2026-08-16 に削除した**（open-gaps #44）

> **⚠️ この節は歴史的な記録。バルクコンデンサはもう基板に無い。**
> 判断の全体は
> [decisions/2026-08-16-remove-bulk-cap.md](decisions/2026-08-16-remove-bulk-cap.md)。
>
> **実測で「守る相手が存在しない」と分かった**（DS1104Z・2026-08-16）:
>
> | | 実測 |
> |---|---|
> | BLE の最大瞬間風速 | **10.22mA**（広告＋スキャンの重なり込み） |
> | 降下 = 10.22mA × 9.2Ω | **94mV** ← **容量ゼロでもこれが上限** |
> | 余裕 300mV に対して | 31%（安全率 3.2 倍） |
> | **µs 級の尖り** | **0 個**（1ns 分解能・60 万点を全数走査） |
>
> 下の「10〜15mA のパルス」は **[暫定]・出典の無い推定値**だった。
> 実測は 10.22mA で、**そもそも µs 級の尖りが無かった**ので、
> 「µs 級の電流変動を supply する」というバルクの存在理由が消えた。
>
> **⚠️ パスコン（1-6）は残る。**役割が違う（ns 級・ループ長で効く）。

当初の設計に無かった。**アルカリ乾電池は消耗すると内部抵抗が上がる。**
BLE の送信は 10〜15mA のパルスで、内部抵抗が上がった電池ではこれが
電圧降下として現れる。

```
新品     内部抵抗 0.15Ω → 15mA で 2mV 降下（無視できる）
末期     内部抵抗 1.5Ω  → 15mA で 23mV 降下
＋接点や配線の抵抗が乗る
```

降下が大きいとマイコンが早期にブラウンアウトし、**電池を使い切る前に
落ちる**。

> **訂正（2026-08-08）。**ここには「バルク容量を入れるとパルスをそこから
> 供給でき、使い切れる領域が広がる。電池寿命そのものが延びる」と書いて
> あったが、**誤り**。降下は「電流 × 内部抵抗」で決まり、**コンデンサでは
> 消せない**。コンデンサが効くのは τ = R×C より短い間だけで、送信バースト
> （数百µs）に対して τ は 40〜150µs しかない。
>
> | 容量 | バースト 300µs での降下 |
> |---|---|
> | 100µF（公称） | 19.5mV |
> | 50µF（DC バイアス後の実効） | 22.1mV |
> | 25µF | 22.5mV |
> | 容量ゼロ（定常値） | 22.5mV |
>
> **容量を倍にしても 3mV しか変わらない。**バルクの役目は、これより速い
> （µs 級の）無線の電流変動を supply することであって、ms 級の降下を
> 減らすことではない。`C15008`（6.3V 品）が DC バイアスで半減しても
> **結論は変わらない**（`test_the_margin_covers_the_transmit_droop`）。

~~100µF（セラミック 47µF ×2 でも可）を 3V3 と GND の間、XIAO の近くへ置く。~~
→ **2026-08-16 に削除**（上の枠）。**パスコンは残る。**

### 1-6. パスコン 0.1µF（**見落としていた項目**）

当初の設計に無かった。**IC の電源端子には必ず入れる。**

| 場所 | 値 |
|---|---|
| XIAO の 3V3 直近 | 0.1µF |
| 74HC595 の VCC 直近（右は 2 個ぶん） | 0.1µF × 個数 |

74HC595 は出力が同時に切り替わるとき電源へノイズを返す。パスコンが無いと
そのノイズが行の入力へ回り込み、**誤検出やチャタリングの原因になる**。

### 1-7. 電池電圧の測定

- 分圧 1MΩ + 1MΩ。3.0V → 1.5V
- 消費は 1.5µA。スリープ電流に対して無視できる
- **スライドスイッチの後ろに置く。** 前に置くと電源を切っても流れ続ける
- 測定点は**ショットキーの手前**（電池側）。USB 接続中も電池電圧そのものが読める
- ADC に入る電圧が VDD を超えないこと。新品 3.2V でも分圧後 1.6V、VDD は 2.8V

---

## 2. キースキャン

### 2-1. 74HC595 の未使用端子（**見落としやすい項目**）

**浮かせてはいけない端子が 2 つある。**

| 端子 | つなぐ先 | 浮かせると |
|---|---|---|
| **MR (10)** マスタリセット | **VCC** | Low で中身が消える。ノイズで勝手にリセットされる |
| **OE (13)** 出力許可 | **GND** | Low で有効。浮くと出力が High-Z になり全キーが反応しない |

未使用の**出力**（左は Q6・Q7、右は Q9〜Q15）は開放でよい。出力なので問題ない。

### 2-2. 右半分は 595 を 2 個数珠つなぎ

最上段が 9 キーあるため 9 列要る。1 個目の **Q7'(9)** を 2 個目の **DS(14)** へ。
SH_CP と ST_CP は共通。

**数珠つなぎは速い打鍵を取りこぼす例が報告されている**（ZMK 公式）。
`spi-max-frequency` を上げて対処する。Task C2-b の重点確認項目。

### 2-3. 行は MCU 直結（変更不可）

ZMK 公式の指示。入力が MCU のピンなら割り込みで起こせるので、常時スキャン
せずに済み電池が持つ。**シフトレジスタは列（出力）専用。**

これは深いスリープの成立条件でもある（`hhkb_split_left.conf` に検証を記録）。

### 2-4. ダイオードはキーごとに 1 個

同時押しのゴーストを止める。実測で確認済み（Task C2-a。ただし**そのときは
1N4007**）。向きは col2row（アノードが列側・カソードが行側）。

**本番は `BAT46W`（ショットキー・SOD-123・LCSC C54110）。**シリコンの
1N4148W は 1mA 未満の VF 最大値が規定されておらず、**電池が減ったときに
行が VIH に届くかを保証できない**（届かないとキーが 1 つずつ反応しなく
なる）。BAT46W は VF ≦ 0.25V @ 0.1mA と IR ≦ 0.3µA @ 1.5V を
**動作点で保証**する唯一の候補。比較と差し戻し先は
[tools/parts.py](../../tools/parts.py)。

---

## 3. 基板

### 3-1. GND ベタ

**両面にベタを敷き、GND につなぐ。**

- 戻り電流の経路が短くなり、放射ノイズと受信ノイズの両方が減る
- BLE の 2.4GHz が乗っているので、基準電位が安定していることは重要
- 熱的にも有利

ベタを入れない理由は無い。

### 3-2. 配線幅

| | 値 | 根拠 |
|---|---|---|
| マトリクス | 0.25mm | 流れるのは数百µA。JLCPCB の最小 0.127mm に対して十分な余裕 |
| 電源 | 0.5mm | 15mA のパルス。太い方が電圧降下が少ない |
| ビア | φ0.6 / 穴 φ0.3 | JLCPCB の標準 |

### 3-3. 取付穴は GND につながない

ケースが樹脂なので意味がない。むしろネジ頭が他所に触れたときの経路になる。
**絶縁のままにする。**

### 3-4. ESD

キーボードは指から静電気が入る。スイッチの端子は列と行に直結している。

TVS アレイを入れる案もあるが、**入れない**。nRF52840 の GPIO には
一定の保護があり、自作キーボードで TVS を入れる例はほとんど無い。
部品点数とコストに見合わないと判断した。**判断であって見落としではない。**

---

## 4. まだ決めていないこと

| 項目 | 決められない理由 |
|---|---|
| 逆流の有無 | **Task C4 の実測待ち。** 逆流するならレギュレータの除去などが要る |
| 電池金具の形状 | 電池室の設計と一体 |
| 子基板の正確な寸法 | ケース奥の内寸を測ってから |

**XIAO の実装位置は決まった** → [子基板の決定](decisions/2026-08-07-daughterboard.md)

基板に部品を置こうとして、**HHKB のキー配列が基板をほぼ埋め尽くしており
XIAO (21×17.8mm) の置き場所が無い**ことが分かった。奥の帯は裏面で 10.3mm
しかない。74HC595 (6.4×10.4mm) と受動部品は入るが、XIAO は入らない。

XIAO だけを小さな子基板に載せ、ケース奥の壁に立てる。USB-C は HHKB と同じ
奥面に出る。本体基板とは 12 本の FFC でつなぐ（行が 5 本渡るので本数が要る）。
信号の並びは [tools/test_daughterboard.py](../../tools/test_daughterboard.py) が
ファームウェアの使用ピンと突き合わせて守る。

---

## 5. 見直して見つかった抜け

この文書を書く過程で、当初の設計に無かったものが 3 つ見つかった。

1. ~~**バルクコンデンサ** — 無いと電池を使い切る前に落ちる~~
   → **2026-08-16 に削除**（#44）。**この「無いと落ちる」自体が、
   出典の無い推定電流（15mA）に乗った誤りだった。**実測 10.22mA では
   容量ゼロでも降下 94mV で、余裕 300mV の内側
2. **パスコン** — 無いと 595 のノイズが行へ回り込む
3. **595 の MR / OE の処理** — 浮かせると動かないか不安定

いずれも「動くかどうか」ではなく「**きちんと動き続けるか**」に効く。
ブレッドボードでは症状が出にくく、基板にしてから気づく類のもの。
