ms0216/hhkb-split/docs/hardware/decisions/2026-08-07-daughterboard.md

# XIAO は子基板に載せ、奥の壁に立てる

**日付**: 2026-08-07
**状態**: 決定（利用者が選択）

---

## 1. なぜ決める必要が生じたか

本体基板に電子部品を置こうとして、**置き場所が無いことが分かった。**

HHKB のキー配列は基板をほぼ埋め尽くす。実測した空きは次のとおり。

| 場所 | 空き | 入るもの |
|---|---|---|
| 基板奥の帯（裏面） | **10.3mm** | 74HC595（6.4×10.4mm）と受動部品 |
| 基板奥の帯（表面） | 5.9mm | 何も入らない（スイッチのピン穴が来る） |
| 基板手前の帯 | 21×18mm が 1〜3 箇所 | XIAO は入るが USB が手前に出る |

導出:

```
プレート上下余白 6.375mm ＋ キーピッチ/2 9.525mm − PCB 内側 3.0mm = 12.90mm
  表面: 12.90 − 7.0（スイッチ本体） = 5.90mm
  裏面: 12.90 − 2.6（ソケット）      = 10.30mm
```

**XIAO は 21×17.8mm。奥の帯には物理的に入らない。**

> **⚠️ 上の 10.3mm は当時（PCB 内側 3.0mm）の数字（2026-08-11 追記）。**
> その後 `PCB_INSET_Y` が 3.0 → 5.3mm になり、奥の帯は **3.40mm**。
> **結論（入らない）はむしろ強化された**が、この表の数字を現在値として
> 別の判断に使わないこと。

---

## 2. 検討した案

| 案 | USB-C の出口 | 追加部品 | 判断 |
|---|---|---|---|
| **子基板を奥の壁に立てる** | **奥面（HHKB と同じ）** | コネクタ 2 個＋ケーブル | **採用** |
| 手前の空きに寝かせる | 手前面か内側面 | なし | HHKB と違う。打鍵時に手の前へケーブルが来る |
| 奥の帯にヘッダでぶら下げる | 奥面 | ヘッダのみ | パッドとスイッチのピン穴の隙間が 0.03〜0.3mm。発注後に判明する類の手戻り |
| ケースを 15mm 深くする | 奥面 | なし | 奥行 108mm という HHKB 再現の根幹を捨てる。却下 |

採用理由は **USB-C の位置が HHKB と同じ奥面になること**。
副次的に、XIAO の抜き差し・書き換え・故障時の交換がすべて楽になる。
JLCPCB は 5 枚無料枠があるので、基板が 1 種増えても費用はほぼ変わらない。

---

## 3. ケーブルに通す信号（12 本）

行は MCU 直結という制約（[keyscan の決定](2026-08-07-keyscan.md)）があるため、
**5 本の行がすべてケーブルを渡る。** これが本数を決めている。

**出所は `tools/circuit.py` の `J_DB` / `J_MAIN`。**この表はそこから写した
ものなので、`test_the_cable_pinout_table_matches_the_circuit` が
1 ピンでも食い違ったら落ちる。**手で直さない。**

| # | ネット | XIAO のピン | 役割 |
|---|---|---|---|
| 1 | `GND` | GND | **地板で受ける**（レーンには載せない） |
| 2 | `V3V3` | 3V3 | **子基板の電源部から本体基板へ供給**（向きが逆になった・#41） |
| 3 | `SPI_MOSI` | D10 | SPI データ |
| 4 | `CS` | D7 | 595 のラッチ。**列の内側を垂直に下ろす 1 本**（D6 の鏡像） |
| 5 | `SPI_SCK` | D8 | SPI クロック |
| 6 | `SPARE2` | D9 | **予備。**用途未定だが配線だけ通す（D4=SPARE の鏡像） |
| 7 | `SPARE` | D4 | **予備。**用途未定だが、後から線は足せないので配線だけ通す（2026-08-14・利用者） |
| 8 | `ROW_A` | D5 | 列の内側・内 |
| 9 | `ROW_B` | D6 | **垂直に降ろす 1 本**（列の内側・真ん中） |
| 10 | `ROW_C` | D3 | 列の外・最も内側 |
| 11 | `ROW_D` | D2 | 列の外・真ん中 |
| 12 | `ROW_E` | D1 | 列の外・最も板端 |

⚠️ **番号は子基板 J_MAIN のもの。本体基板 J_DB では 13−n 番**（2026-08-28・[open-gaps #19](../open-gaps.md)）。J_DB は口を奥向き（子基板側）にするため裏面で 180° 回してあり、ピン 1 が −X 側にある。ケーブルはまっすぐな A タイプなので、同じ導体は J_MAIN の n 番と J_DB の 13−n 番に着く（例: GND は J_MAIN 1 番・J_DB 12 番）。`test_the_two_boards_agree_on_the_cable` がこの鏡像を検査する。

⚠️ **行のネット名は「行番号」ではなく「ケーブル上の位置」**（2026-08-15・
利用者「DB の ROWx というピン名前付は不適切になるかもしれません」）。
**どの行を載せるかは左右で違う**ので、`ROW2` のような名前を付けると
左では行 2、右では行 4 を運ぶ嘘の名前になる。

行番号との対応は**左右の overlay の `row-gpios`**（並び順が行番号）が
唯一の出所で、`matrix.row_nets(half)` が読む。

**並び順を決めたのは配線の都合。** 子基板では FFC が手前、XIAO のパッドが
左右 2 列にある。手前から上がる配線は、近いパッドへ行くものほど外側を通す
必要があり、ピン順がそれと逆だと交差する。**最初の並びでは 6 箇所が短絡した。**

**2026-08-14 に並びを作り直した**（open-gaps #41）。効いた条件が 2 つある。

1. **主基板側**: 行バスは J_DB の上下へ伸びるので、素朴に行番号の昇順で
   並べると上下 2 群が交差する。**2026-08-15 に考え方を改めた**（利用者）:
   **J_DB から遠い行ほど、パッド列で「板の内側」の枠へ。**遠くまで行く枝を
   内側に置くと、他の枝を跨がずに列を離れられる。
   **左右で並びが逆になる**——J_DB が左は板の右端・右は左端にあり、
   同じ 12 番でも板端／内側の意味が入れ替わるため。
2. **子基板側**: レーンの規則（近いパッドほど外側）を満たす必要がある。
   **その順序のズレは XIAO のピン割り当て＝ファームで吸収する**
   （利用者の判断「配線でひねるのではなくソフトで受けるべき」）。
   （当時の記述: 9 番が ROW4→D4、11 番が ROW2→D6 と入れ替わっていた。
   **この ROWn は 2026-08-15 に廃した旧い名前**——上の表を見ること。）

**行 4 は D9 から D5 相当（左列）へ戻した**（当時の名前で ROW4）。右列へ逃がしていたのは
「左列のレーンが 6 本だとアンテナの真下を 2 本通る」ため（#23）だが、
**その 6 本目は VBATT_SENSE だった。**分圧が子基板へ移って FFC を
渡らなくなったので、行 5 本を左列に戻しても 5 本のまま。
→ ファームの `&spi2_default`（MISO 外し）も**不要になって削除した。**

**2026-08-14 に並びを左右対称へ組み替えた**（利用者「D1〜D6 を完璧に真似る
形で、左右対称に」）。XIAO は x=150.0 を挟んで左右対称なので、FFC も
n ↔ 13-n で写る。左の D4→7 / D5→8 / D6→9 / D3→10 / D2→11 / D1→12 が、
右では D9→6 / D8→5 / D7→4 / D10→3 / 3V3→2 / GND→1 になる。

⚠️ **この組み替えで GND が 2 本から 1 本に減った。**GND はレーンに載せず
地板で受けると決めたため（載せると FFC まで 1 本の細線で運ぶ形になる）。
**SCK から最寄りの GND までが 0.5mm → 2.0mm に伸びている。**効くのは
遷移が速い SCK 1 本で、ROW はゆっくりなので影響は小さい。
**どれだけ悪化するかは実測していない。**

問題が出たときの逃げ道は決めてある: **D9(SPARE2) を両基板で GND へ
ジャンパする**と、SCK(5) の隣が GND に戻る。そのために SPARE2 は用途
未定のまま配線だけ通してある。主基板側は J_DB の 6 番の近くに GND の
テストパッドを置いておくと後から楽になる。

**両端を GND にはできなかった。**12 番は GND だが、1 番は CS になっている。
上の配線順の制約が先に決まるため、両端を GND にすると交差が戻る。CS は
1 スキャンに 1 回しか動かない最も遅い信号なので、端に置く害が最も小さい。
（この文書は以前「両端を GND にしてある」と書いていたが、**事実と違った。**
表そのものも旧い並び順のまま残っていた。）

### コネクタ

**12 ピン・0.5mm ピッチの FFC（フレキケーブル）コネクタ**を両基板に置く。
型番は `Hirose FH12-12S-0.5SH`（JLCPCB 在庫あり・$0.68）。
`test_the_connector_spec_matches_the_board` が実基板と照合する。

- 厚みが 1mm なので、ケースの限られた高さを食わない
- 12 本が 6mm に収まる

（この節は以前「1.0mm ピッチ」「12 本が 12mm」と書いていた。**実基板は
最初から 0.5mm ピッチだった。**本数だけを見る検査があったので通っていた。）
- JLCPCB の実装工程で載る（利用者が半田付けするのはソケットだけ、という方針を保てる）
- ケーブルは既製品

**入手できなかった場合の代替**: 12 ピン 2.54mm ピンヘッダ＋リボンケーブル。
高さを 8.5mm 食うので、ケース内の余裕を確認してから。

---

## 4. どちらの基板に何を載せるか

### 本体基板（裏面・奥の帯）

| 部品 | 個数 | 置く理由 |
|---|---|---|
| 74HC595 | 左 1 / 右 2 | **駆動する列のすぐ隣。**配線が最短になる |
| 0.1µF パスコン | 595 の個数ぶん | 各 595 の VCC 直近 |
| 100µF バルク | 1 | 電源部 |
| ショットキー SB240LES | 1 | 逆流防止＋ USB 時の電池切り離し |
| 1MΩ ×2 | 1 組 | 電池電圧の分圧 |
| スライドスイッチ | 1 | 電源 |
| 電池線のランド | 2 | 単3×2 の電池ボックスから |
| FFC コネクタ 12P | 1 | 子基板へ |

### 子基板

| 部品 | 個数 |
|---|---|
| XIAO nRF52840（**プロトタイプ期はピンソケット**。~~直付け~~。下の追記を読むこと） | 1 |
| 0.1µF パスコン | 1 |
| FFC コネクタ 12P | 1 |
| ケース固定用の穴 | 2 |

**子基板は奥の壁の内側に立てる。** USB-C は壁の切り欠きから覗く。
HHKB と同じく、少し奥まった位置になる。

> **⚠️ 2026-08-12 訂正: XIAO は「着脱可」にできない。**
> ### ⚠️ 2026-08-12 追記 **この判断は覆っている（プロトタイプ期のみ）**
>
> 利用者が **プロトタイプ期はピンソケットを採用**すると決めた（#27）。
> **下の 0.72mm を承知のうえ**での判断で、理由は「基板到着後もまだ試作の
> 域を出ず、XIAO を何度も着け外しする」から。**脱プロトタイプで直付けへ
> 戻し、ケースを刷り直す。**部品は FHU-1x40SG-Y（秋月 110302・座高 8.5mm）で、
> `DB_SOCKET_SEAT` = 8.5 / `DB_XIAO_LIFT` = 10.5mm。
> アンテナの件は open-gaps #23 と #27、部品は parts-audit.md #10 を見ること。
>
> ピンソケットを挟むと XIAO ごとアンテナが浮き、**本体基板の地板との
> 距離が 7.22mm → 0.72mm**（指針 5〜10mm）になる。低背ソケットでも
> 1.67mm で足りない。**浮きの上限は 2.24mm**（open-gaps #27）。
> `test_the_antenna_keeps_its_distance_from_the_main_board` が見張る。
> **故障したら子基板ごと作り直し**（$25〜35・2〜3 週間。本体基板 2 枚と
> ケーブルは無傷）。

---

## 5. ケースへの影響

| 変更 | 内容 |
|---|---|
| 奥の壁に USB-C の切り欠き | 幅 10mm × 高さ 5mm 程度。プラグの外形が入る大きさ |
| 子基板の取付ボス 2 本 | 奥の壁の内側 |
| 電池室の位置 | 子基板と干渉しないこと。奥の壁から 25mm は空ける |

**ケースの外形寸法（奥行 108mm・手前端 17.5mm・傾斜 7.3°）は変えない。**
これが変わらないことが、この案を採った理由そのもの。

---

## 6. まだ決めていないこと

| 項目 | 決められない理由 |
|---|---|
| 子基板の正確な高さ・幅 | ケース奥の内寸を測ってから |
| FFC の長さ | 同上 |
| 電池室と子基板の位置関係 | ケースを作り直すときに一緒に決める |
