ms0216/hhkb-split/docs/hardware/decisions/2026-08-16-cdb-has-no-local-load.md

# 2026-08-16 調査 C_DB は「負荷の直近にいないパスコン」だった（削除できる）

> **ファイル名は `cdb-has-no-local-load` のままだが、正確には
> 「no local load」ではなく「負荷はいるが、その直近が C_DB ではない」。**
> 初版の理由づけが誤っていた名残（下の警告を読むこと）。

> ### ✅ 2026-08-16 **削除を実施した**（open-gaps #45）
>
> この文書は調査の記録。**結論は独立に再検証したうえで実行に移した。**
> 実装部品が **2 個減**（左右の子基板に 1 個ずつ）。
> **子基板にコンデンサは 1 つも無くなった**（C_BULK は #44）。
>
> 再検証したもの（§7 の「まだやっていないこと」に対する答え）:
>
> | 検証 | 方法 | 結果 |
> |---|---|---|
> | §1 子基板 V3V3 は 4 パッド | `.kicad_pcb` を footprint ブロックで走査 | **一致** |
> | §2 XIAO 内部 2.2µF ×5 | Seeed の `.kicad_pcb`（73 footprint）を**自分で数え直した** | **完全一致**（12 部品 / 20 パッド） |
> | §3 分流比 58:1 | 2π·167MHz·145nH = 152Ω ÷ 2.6Ω | **一致** |
>
> 削除後の DRC: **子基板 違反 0 / 未配線 0 / 警告 0。**
>
> 触った先は §7 の表のとおり。**壊し方の検査も入れた**（作法 2）:
> `test_the_daughterboard_has_no_part_that_needs_local_decoupling`
> ——「子基板に 595 を足す」で落ちることを `test_the_rules_actually_bite`
> で確かめてある。

**調査結果（実施済み・下は調査当時の記述）。**`C_DB`（0.1µF・C49678・0805）は
子基板の 3V3 に載っているが、**その 3V3 に急な電流を要求する負荷は、
すべて XIAO の内部にいて、内部のパスコン群のほうが C_DB より
桁違いに近い**ことが分かった。**C_DB の取り分は誤差**なので削除できる。

**覆した結論**: #40「XIAO → C_DB」（各 IC が自分の直近パスコンを持って
いるから C_RAIL を消してよい、という論拠の一部）。
**C_DB は「XIAO のパスコン」ではなかった。**XIAO はモジュールで、
**負荷（nRF52840）も、それを見るパスコンも、両方とも内部にいる。**

> ### ⚠️ この文書は理由づけを 1 度書き直している（2026-08-16・利用者の指摘）
>
> **初版はここに「3V3 に電流を引く能動部品が子基板上に 1 つも無い」
> 「XIAO は 3V3 の供給側で、負荷ではない」と書いていた。これは誤り。**
>
> **USB 駆動時しか見ていなかった。**電池駆動時は
> `電池 → SW_PWR → D_PWR → V3V3 → XIAO` で、**3V3 は XIAO への入口**。
> その先の nRF52840 は BLE 送信で電流をステップさせる**実在の負荷**である
> （`circuit.py:496` の `D_PWR: A=VBATT_SW, K=V3V3`）。
>
> | | 3V3 の向き | XIAO は |
> |---|---|---|
> | USB 駆動 | 内部 LDO が生成し**外へ出る** | 供給側 |
> | **電池駆動** | ショットキー経由で**中へ入る** | **負荷側** |
>
> **結論（削除できる）は変わらないが、根拠は下のとおり差し替えた。**
> 片方の動作モードだけ確かめて全体のように言った——この案件で
> 繰り返し出ている型そのもの（`never-report-a-named-subset-as-the-whole`）。

### 正しい理由づけ — 「相手がいない」ではなく「取り分が誤差」

```
        ┌─ C_DB（0.1µF）… XIAO の外側
        │
D_PWR ──┴──── XIAO の 3V3 ピン
                    │  ← ここから内側は XIAO の中
                    ├─ 2.2µF ×5（内部・分散配置）
                    └─ nRF52840（負荷。急な電流はここが要求する）
```

**電流は「近い順」に取られるのではなく、全供給元から同時に、
ループインダクタンスに反比例して分流する。**C_DB も流していないわけ
ではない——**取り分が数 % 以下で、誤差になる**というだけ。

**したがって「閾値」は無い。**もし C_DB が内部の 5 個と同じ距離に置けたなら
同格に効く。効かないのは**外側だから**ではなく、**ループ長の差が桁違い**だから。

そして**足りているところに数 % を足しても改善しない**一方、**もし内部が
不足していたなら数 % では救えない**。**どちらに転んでも C_DB の出番が無い。**

**きっかけは利用者の指摘**（2026-08-16）:

> 外に出る 3V3 を守るために、595 のパスコンがあるのでは？
> 595 を守るために、595 から遠い C_DB がある意味は？
> XIAO 内部の、調査してくれたコンデンサたちがパスコンなのでは？

**両方とも正しかった。**

---

## 1. 実測 — 子基板の 3V3 ネットに載っている全パッド

`pcb/hhkb_split_daughterboard.kicad_pcb` を機械的に走査した（4 件が全数）。

| 部品 | 座標 | パッド | 3V3 に対する役割 |
|---|---|---|---|
| `U_MCU` | (150.00, 92.95) | `3V3` | **双方向。**USB 時は供給源（内部 LDO の 3V3_OUT）、**電池時は入口**（その先の nRF52840 が負荷） |
| `D_PWR` | (151.51, 90.45) | `1` | ショットキー。**電池はここから 3V3 へ入る**（`A=VBATT_SW, K=V3V3`） |
| `C_DB` | (155.40, 89.50) | `1` | **問題のパスコン** |
| `J_MAIN` | (150.00, 111.0) | `2` | FFC で主基板の 595 へ渡す |

**子基板の「板の上」には、急な電流を要求する能動部品が 1 つも無い。**
⚠️ **これは「負荷が無い」という意味ではない**（初版はそう書いて誤った）。
負荷は 2 つとも**この板の外**にいる:

| 負荷 | どこ | C_DB から見て |
|---|---|---|
| nRF52840 | **XIAO の内部** | 内部の 2.2µF ×5 が**桁違いに近い**（§2） |
| 595 ×2 | **主基板** | **直近に `C_U1`/`C_U2` がいる。**C_DB 側の取り分は **1/58**（§3） |

**どちらも、自分の直近に別のパスコンを持っている。**
C_DB は両方に対して**外側**にいる。

⚠️ **接頭辞で走査していない**（CLAUDE.md の作法 6）。
footprint ブロックごとにパッドのネット名を読んで数えた。

## 2. XIAO 内部（**KiCad ソースのネットリストから全数**）

出典（参考・版 1/2 で使った）: [Seeed_Studio_XIAO_nRF52840_PDF.pdf](https://files.seeedstudio.com/wiki/XIAO-BLE/Seeed_Studio_XIAO_nRF52840_PDF.pdf)
（v1.1・2025-12-19・3 ページ）。

⚠️ **この節は 2 回間違えた。読み方を 2 段階で直した記録として残す。**

| 版 | 読み方 | 何を書いたか | 判定 |
|---|---|---|---|
| 1 | `pdftotext -raw` の文字列 | `C39/C41/C42` を「LDO 入出力」とまとめた | **誤り。**文字列抽出は座標の近さしか教えず**結線が読めない** |
| 2 | PDF をレンダリングして目視（作法 7） | 「LDO 出力は **C3** 単独」「C39 は LDO と無関係」 | **まだ誤り。**U6 の隣の 1 個しか読めていなかった |
| **3** | **KiCad ソースのネットリストを機械で数えた** | **下の表** | **これが正** |

**教訓: 目視は取りこぼす。**作法 7「見えるものは見る」に従って
レンダリングしたが、**絵は「見えた範囲」しか答えない。**
離れて置かれた同じネットの部品は目に入らない。
**数えられるものは機械で数える**——ネットリストは全数を返す。

出典（版 3）: Seeed 公式の KiCad ソース
`Seeed-Studio-XIAO-nRF52840_V1.1_SCH & PCB_251222_01/`。
⚠️ **`.kicad_sch` は Eagle 取り込みで wire が 0 本**なので結線が無い。
**`.kicad_pcb`（73 footprint）のパッドのネット名**を footprint ブロック
ごとに読んだ（接頭辞で走査していない・作法 6）。

```
VBAT →[Q1 LP0404N3T5G]→ VIN →[U6 SGM2040-3.3 IN/OUT]→ 3V3
                         │                              │
                        C4 2.2µF          C3/C6/C29/C39/C41 = 2.2µF ×5
```

**3V3 ネットの全パッド（20 パッド / 12 部品・全数）:**

| 部品 | 値 | 位置づけ |
|---|---|---|
| U6 SGM2040-3.3YUDH4G | 3.3V / 250mA LDO | **3V3 の発生源**（pad 1 = OUT） |
| **C3 / C6 / C29 / C39 / C41** | **2.2µF ×5** | **LDO の出力容量。公称 合計 11µF** |
| U1 NRF52840_QF | — | **唯一の実負荷**（6 パッド） |
| R13 / R5 | 10k / 2.2k | プルアップ等 |
| RGB6 | RGB | LED |
| U7 | **DNP** | 未実装 |
| U4 XIAO-nRF52840 | — | モジュール外形（3V3 の出口） |

C4(2.2µF) は VIN 側で**別ネット**。C34/C42 は `DEC4-6`、C24/C35 は RF 系で、
いずれも 3V3 ネットではない（**版 1・2 はここを混ぜていた**）。

> **⚠️ 「合計 11µF」と足し算で読まないこと。効いているのは並列であること。**
>
> パスコンとしての速さを決めるのは容量ではなく **ESL（等価直列
> インダクタンス）**で、これは**並列にすると下がる**（5 個なら約 1/5）。
>
> | | 容量 | ESL | ns 級に応えられるか |
> |---|---|---|---|
> | 11µF **1 個**（大パッケージ） | 11µF | 大 | **応えられない** |
> | **2.2µF ×5（分散）** | 11µF | **約 1/5** | **応えられる** |
>
> **同じ 11µF でも中身が違う。**Seeed が 1 個にせず 5 個へ散らしているのは
> この定石。**LDO の安定条件（§4-1）には合計値が効き、nRF52840 の
> パスコンとしては並列数が効く**——2 つは別の話で、両方とも満たされている。

**XIAO 内部の 3.3V レールに載っている実負荷は nRF52840（U1）だけで、
そのパスコンは内部に全部揃っている。**3V3 に 2.2µF が 5 個並列で載り、
別ネットの `DEC4-6`（C34/C42）が nRF52840 の内部レギュレータを見ている。

**負荷が内部にいて、そのパスコンも内部にある。**
外から 0.1µF を 1 個足しても、分流の取り分は誤差にしかならない。

## 3. なぜ C_DB は 595 の役に立たないか

### 理由は「595 が自分の直近に `C_U1` を持っているから」

595（`U1` / `U2`）と `C_U1` / `C_U2` は**主基板側**にある。
子基板の部品は `BT1_-` `C_DB` `D_PWR` `H1` `H2` `J_MAIN` `R_HI` `R_LO`
`SW_PWR_1` `U_MCU` の 10 点で、595 は含まれない。

595 のエッジ電流は、**`C_U1` / `C_U2` が主基板上で局所的に閉じる。**
C_DB へ回ってくるのは、その分流の残りでしかない。

桁を出した（[2026-08-16-ffc-loop-inductance.md](2026-08-16-ffc-loop-inductance.md)。
**机上の見積もりで実測ではない**）:

| | 値 |
|---|---|
| 595 のエッジ（t_r 2〜3ns）の knee 周波数 | 167〜250 MHz |
| `C_U1` の局所枝 \|Z\| @167MHz | **2.6 Ω** |
| XIAO 3V3_OUT → 595 の直列 L（**145nH**）の \|X_L\| @167MHz | **151 Ω** |
| **分流比** | **C_U1 : C_DB 経路 = 58 : 1** |

**エッジ電流の 98% 以上が主基板上で閉じ、C_DB へ来るのは 2% 未満。**
C_DB は 595 のエッジに対して事実上見えていない。

### ⚠️ **「FFC が挟まっているから」ではない**

**この節は当初「ns 級のループは FFC を渡れない」と書いていた。
数字としては正しいが、理由づけとして不正確だった**（2026-08-16 に訂正）。

145nH の内訳は **FFC 64nH（4 割）＋ 両基板の 0.2mm 幅 V3V3 配線 81nH（6 割）**。

> **FFC を 0mm にしても 81nH が残り、分流比は 30:1 以上。結論は動かない。**

つまり**この節の結論は FFC の存在に依存していない。**
依拠しているのは **595 が自分の直近にパスコンを持っていること**のほうで、
**FFC のインダクタンスという論拠は、そもそも必要でなかった**（同文書 §5）。

⚠️ **ついでに分かったこと**: 支配的なのは FFC ではなく
**自分の基板の V3V3 トレース**（子基板 28.3mm ＋ 主基板 68.4mm ＝ 97mm を
0.2mm 幅で引いている。GND はベタなのに片道だけ細い）。
**いま直すべき不具合ではない**——58:1 は十分すぎる——が、
**事実として知っておくもの**（同文書 §1・§3）。

パスコンで効くのは距離ではなく**往復ループ長**（`decoupling-cap-is-loop-length-not-distance`）。
C_DB のループ長 4.49mm は XIAO の 3V3/GND パッドに対する値で、
595 に対しては上の 145nH が丸ごと乗る。

## 4. LDO の負荷過渡は C_DB では担えない

残る可能性は「595 の消費電流がステップで変化したとき、FFC 越しの
負荷変動に対して SGM2040 の出力が振れる」ぶん。**これも C_DB の
担当ではない。**

| | 帯域 | C_DB(0.1µF) は効くか |
|---|---|---|
| LDO のループ帯域 | 数十〜数百 kHz | **効かない**（19MHz 品） |
| ここに効かせるなら | µF 級が必要 | **#44 で「守る相手が実在しない」と実測済み** |

二重に、C_DB が埋められる穴ではない。

### 4-1. SGM2040 の出力容量は XIAO 内部で満たされている（2026-08-16 追記）

**この節にはもともと穴があった。**「負荷が近くにいない」は
「**LDO 自身が外部の出力容量を安定条件として当てにしていないか**」を
別に確かめないと削除の根拠にならない。C_DB は XIAO の 3V3_OUT 直近＝
**LDO 出力の直近でもある**からで、そこは埋めた。

出典: [SGM2040 データシート](https://www.sg-micro.com/rect/assets/9d7e04e6-7450-4c5c-b94c-fa500b90b628/SGM2040.pdf)
（SG Micro・18 ページ）。XIAO 実装品 `SGM2040-3.3YUDH4G/TR` と**型番が完全一致**
（Ordering Information の UTDFN-1×1-4AL 版）。

| 出どころ | 規定 |
|---|---|
| Recommended Operating Conditions | Output Effective Capacitance, C_OUT = **0.1µF 〜 10µF** |
| OUT ピン説明 | 「effective capacitance in the range of 0.1µF to 10µF **to ensure stability**」「**as close as possible to OUT pin**」 |
| Application Information | 「0.22µF or larger X7R/X5R」「**minimum effective capacitance of C_OUT that SGM2040 can remain stable is 0.1µF**」 |

**§2 の 2.2µF ×5（公称 11µF）が、これを内部で満たしている。**

| | 判定 |
|---|---|
| 安定条件 | 公称 11µF。**下限 0.1µF に対し 100 倍以上。C_DB は安定性に不要** |
| 上限側 | **公称値では 10µF 上限を既に超えている。**C_DB(0.1µF) を足す余地はどこにも無い——**足す側が危ない** |
| DC バイアス減衰（§8 の懸念） | **むしろ好都合。**実効値は公称より下がるので 10µF 上限側に収まる。下限 0.1µF に対しては 5 個並列ぶんの余裕がある |

⚠️ **上限側は公称値で超えている**が、SG Micro が XIAO のような
使い方を想定していないとは考えにくく、実効値（DC バイアス・温度で目減り）
では収まっている公算が大きい。**いずれにせよ C_DB を足す方向の議論は
成立しない**ので、削除の判断には影響しない。

**C_DB は、その 5 個並列に 6 個目を足す行為。**C_RAIL が C_U1 の重複だったのと同じ形（§5）で、
今回はそれが**外部データシートで裏を取れている**。

## 5. #40 との関係 — **同じ性質のものが、もう 1 つ残っていた**

#40 で `C_RAIL` を消したときの論拠はこうだった:

> 削除した理由は「不要と証明できたから」ではない。必要と言える根拠が
> 1 つも無く、**各 IC が既に自分の直近パスコンを持っているから**
> （595 → C_U1/C_U2、**XIAO → C_DB**、レール → C_BULK 100µF）

**この括弧の中の「XIAO → C_DB」が誤りだった。**XIAO は IC ではなく
モジュールで、パスコンは内蔵している。C_DB は XIAO の外側に付いた
**重複**であって、C_RAIL が C_U1 の重複だったのとまったく同じ形。

| | C_RAIL（#40 で削除） | **C_DB（今回）** |
|---|---|---|
| 名目上の役割 | ケーブル入口の高周波を落とす | XIAO のパスコン |
| 実際 | C_U1 の 5.1mm 隣＝重複 | **XIAO 内蔵の 2.2µF ×5 の重複。負荷はいるが、その直近は内部の 5 個** |
| 削除の論拠 | 必要と言える根拠が無い | 同上 |

## 6. #44（バルク削除）との関係

**別件。#44 が消したのは µs 級を担当する `C_BULK` で、根拠は
「BLE の最大瞬間風速が実在しなかった」という実測だった。**

今回の根拠は電流ではなく**トポロジ**（負荷が近傍に無い）。
#44 の §6「パスコンは残る・役割が違う」は**バルクとパスコンの
役割の違いについては今も有効**だが、**C_DB が守っている相手が
誰なのかは #44 では検証していない。**そこが今回埋まった。

## 7. 結論と、まだやっていないこと

**C_DB は削除できる。**根拠は 2 つで、**両方とも外部の事実で裏が取れている**:

1. **3V3 の負荷は 2 つとも子基板の外にいて**（XIAO 内部の nRF52840・
   主基板の 595）、**どちらも自分の直近に別のパスコンを持っている**。
   C_DB は両方に対して外側で、**分流の取り分が誤差**（§1・§2・§3）
2. **LDO の安定条件も XIAO 内部で満たされている**（§4-1・データシートの
   C_OUT 規定と内部の 2.2µF ×5＝公称 11µF）

実装部品が **2 個減る**（左右の子基板に 1 個ずつ）。

**✅ 2026-08-16 に削除を実施した**（冒頭の追記）。手順は #40 と同じで、
**消した名前で grep して 3 つを揃えた**（CLAUDE.md の作法 8）。
実施後の確認:

```
grep -c C_DB pcb/hhkb_split_daughterboard.kicad_pcb          →  0
grep -c C_DB pcb/unrouted/hhkb_split_daughterboard.kicad_pcb →  0
grep -c C_DB pcb/hhkb_split_daughterboard.kicad_sch          →  0
grep -c C_DB pcb/drc_daughterboard.json                      →  0
grep -c C_DB pcb/route_daughterboard.json                    →  0
```

子基板の回路図は部品 8 → **7 個**。DRC は **違反 0 / 未配線 0 / 警告 0**。

⚠️ **`tools/` のコメントには C_DB の名前が残っている**が、これは
**「なぜそこに置いていたか」「なぜ消したか」の記録**として意図的に
残したもの（配線コードの形を説明している）。**生きた定義は 0 件。**

| | 触るもの |
|---|---|
| コード | `tools/circuit.py:599` のネットリスト、`tools/gen_daughterboard.py` の配置（`c.SetReference("C_DB")` 周辺・`SILK_REF` の 739 行目）、`tools/gen_sch.py:105` と `:472` |
| 検査 | `test_every_ic_has_a_decoupling_capacitor` の `ICS`（`circuit.py`）から `xiao_nrf52840` を外す。**「モジュール内蔵で充足」を記録として残す**——外すだけだと、次に誰かが「XIAO にパスコンが無い」と言って足し直す |
| 生成物 | `pcb/hhkb_split_daughterboard.kicad_pcb`、`pcb/unrouted/...`、`.kicad_sch`、`pcb/drc_daughterboard.json`、`pcb/route_daughterboard.json` |
| 記録 | この文書、`open-gaps.md` #40 の「XIAO → C_DB」、`parts-audit.md` §5、`decisions/2026-08-16-remove-bulk-cap.md` §6 の「パスコンは全部残る」 |

**壊し方の検査**（作法 2）は「C_DB が復活していないこと」ではない。

⚠️ **初版はここを「3V3 に子基板側の負荷が増えていないこと」と書いていたが、
これも「負荷が無い」という誤った前提の上に載っていた**（負荷は最初から
2 つあり、どちらも板の外にいる）。**正しくは:**

> **「子基板の板の上に、自分の直近パスコンを持たない能動部品が
> 現れていないこと」**

**数えるべきは負荷の有無ではなく、「その負荷の直近に誰かいるか」。**
後から子基板へ 3V3 で動く IC を足したら、**その IC 自身の隣に**
パスコンが要る（C_DB の位置に戻すのではなく）。

## 8. 未確認のまま残るもの

| | 状態 |
|---|---|
| **LDO の出力容量の規定と、それを満たす内部部品** | **確認済み**（2026-08-16・§4-1）。C_OUT = 0.1〜10µF に対し内部は 2.2µF ×5＝公称 11µF。**この節にこの行が無かったことが、最初の版の穴だった** |
| XIAO 内蔵パスコンの実効値（DC バイアス・温度で目減りする） | **未確認**。データシート上の値のみ。ただし**安定性の判断には効かない**——公称 11µF は下限 0.1µF に対し 100 倍以上で、目減りは 10µF 上限側にはむしろ好都合（§4-1） |
| 3V3 の ns 級リプルの実測 | **未実施**（オシロが要る・`provisional-values.md` と同じ制約） |
| FFC 越しのループインダクタンス | **机上で見積もり済み・実測は未**（2026-08-16・[2026-08-16-ffc-loop-inductance.md](2026-08-16-ffc-loop-inductance.md)）。XIAO 3V3_OUT → 595 で **約 145nH（150nH の桁）**。うち FFC は 64nH＝4 割で、**残りは両基板の 0.2mm 幅 V3V3 配線**。§3 の結論は支持されたが、**根拠は FFC ではなく C_U1 の局所ループだった**（同文書 §5） |

いずれも「C_DB を足せば直る」たぐいのものではない（§3・§4）ので、
削除の判断は上の 3 つを待たない。
