ms0216/hhkb-split/docs/hardware/decisions/2026-08-16-xiao-antenna-ground-from-seeed-source.md

# XIAO nRF52840 v1.1 の実基板から読んだ ANT1 周りの地板構成（2026-08-16）

**#23 を閉じるものではない。**#23 の本体は手 0（アルミ箔で RSSI・§6-6b）で、
これは**測る前に無料で分かることを増やしただけ**。ただし**判定基準そのものに効く。**

## 出典（すべて機械で数えた。目視ではない）

```
/Users/m/Downloads/Seeed-Studio-XIAO-nRF52840_V1.1_SCH & PCB_251222_01/
  Seeed Studio XIAO nRF52840 v1.1.kicad_pcb   （version 20241229・73 footprint）
```

読み方は**フットプリント単位でパッドのネット名を読む**（接頭辞での走査をしない・
CLAUDE.md 作法 6）。ベタは `filled_polygon` の実座標、配線は `segment` の
始点・終点・幅、ビアは `via` の座標と径。**全部を点で判定して、
アンテナ本体の矩形からの距離を出した。**

回路図（`02 XIAO Header & nRF52840.kicad_sch`）は Eagle からの取り込みで
**wire が 0 本**なので結線が読めない。**結線はすべて `.kicad_pcb` 側で読んだ。**

## 基板と ANT1 の位置

| | 値 |
|---|---|
| 基板外形（Edge.Cuts の bbox） | x 138.0236〜158.9786 / y 96.1136〜113.8936（**20.955 × 17.780mm**） |
| 層構成 | **4 層**（F.Cu / In1.Cu / In2.Cu / B.Cu） |
| ANT1 | `ANT-SMD3P-3.2X1.6X1.04MM` / Value `ANTENNA-AN3216` |
| ANT1 の原点・回転 | (139.095479, 103.205275) / 180° |
| ANT1 の本体矩形（1.6 × 3.2mm） | **x 138.295〜139.895 / y 101.605〜104.805**（長辺が y 方向） |
| F.CrtYd | local x −0.762〜0.762 / y −1.651〜1.651 |

**モジュール外縁からアンテナまでの距離: 0.271mm**
（アンテナ本体 x=138.295 − 基板外形 x=138.0236）。
つまり **Seeed はアンテナを基板の外周ぎりぎりに置いている。**

## パッドとネット（ANT1 のフットプリントから直接）

| パッド | 形 | グローバル座標 | サイズ | ネット |
|---|---|---|---|---|
| 1 | smd roundrect | 139.565, 104.805 | 0.65 × 0.7 | `Net-(ANT1-S)`（**給電**） |
| 2 | smd roundrect | 138.625, 104.805 | 0.65 × 0.7 | `GND` |
| 3 | smd roundrect | 139.095, 101.605 | 1.6 × 0.7 | `Net-(ANT1-Pad3)`（**調整用スタブ**） |

## ★ 実測: 全層の禁止域（**これがいちばん効く数字**）

アンテナ本体矩形の外側へ 5° 刻みで放射状に探索し、
**最初に銅（配線・ビア・パッド・ベタ）に当たるまでの距離**を層ごとに出した。
さらに行ごとに「x を外形から増やして最初に銅が現れる x」を 0.02mm 刻みで走査した。

| 層 | アンテナの y 範囲での銅の先端 x | **外形からの奥行** | 何が来るか |
|---|---|---|---|
| **F.Cu** | 138.30 | 0.28mm | ANT1 自身のパッドと Pad3 スタブ（**アンテナ由来のもの以外は 141.16 まで無い**） |
| **In1.Cu** | **141.16** | **3.14mm** | GND ベタ |
| **In2.Cu** | **141.16** | **3.14mm** | GND ベタ |
| **B.Cu** | **141.16** | **3.14mm** | GND ベタ |

**禁止域は 4 層とも同一の矩形で、`x < 141.16`。**
y 方向は 99.5〜107.0 の全域（＝**アンテナ端の基板幅を丸ごと**）で銅が無い。

> **禁止域のサイズ: 3.14mm（奥行）× 7.6mm（幅・基板の全幅）・全 4 層共通。**
> アンテナ**本体の縁**から数えると、内側（+x）方向へ **1.30mm**。
> 斜め 45° で 1.87mm、真横（±y）で 2.60mm。

**In1/In2/B の 3 層はアンテナの y 範囲で完全に同じ形をしている**
（行ごとの先端 x が 3 層とも 141.16 で一致）。つまり
**Seeed は「アンテナ端の 3.14mm を、内層 2 枚と裏面から全部抜く」**という
作り方をしている。

### アンテナ直下・裏面の銅

**無い。**B.Cu・In1.Cu・In2.Cu とも、アンテナ本体矩形（x 138.295〜139.895）の
真下には銅が 1 つも無い（先端が x=141.16 なので 1.265mm 手前で終わっている）。
F.Cu にあるのは ANT1 自身のパッド 3 つと、Pad3 に繋がる調整スタブだけ。

## 給電線とマッチング（実配線から）

| | 実測 |
|---|---|
| 給電線の層 | **F.Cu のみ**（内層を通っていない） |
| 給電線の幅 | **0.293368mm**（3 区間とも同一。約 11.5mil） |
| 経路 | パッド1 (139.565,104.805) → 直線 0.960mm ↑ → **円弧**（mid 139.789,106.304）→ (140.327,106.528) → 直線 0.363mm → (140.691,106.528) → 直線 0.508mm → (141.199,106.528) |
| **給電線の全長** | **約 2.7mm**（直線 0.960 + 0.363 + 0.508 ＝ 1.831 ＋ 円弧 約 0.85） |

**直角を避けて円弧で曲げている。**

### マッチング回路（ANT1 のネットに繋がる部品を全走査して抽出）

| 部品 | 値 | 座標 | 繋がっているネット | 役割 |
|---|---|---|---|---|
| **C37** | **0.5pF** | 140.691, 106.782 | `Net-(ANT1-S)` / `GND` | **シャント C**（給電線から GND へ） |
| **C38** | **4.7nH** | 141.453, 106.528 | `Net-(ANT1-S)` / `Net-(U1-ANT@H23)` | **直列 L**（nRF52840 の ANT ピンとの間） |
| **C10** | **1nF** | 139.090, 99.875 | `Net-(ANT1-Pad3)` / `GND` | **Pad3 の調整スタブを GND へ落とす** |

> **C36 はマッチングではない。**ANT1 のどのネットにも繋がっていない
> （x=142.2146 にある別系統）。**部品番号の近さで推測せず、ネットで判定した。**

つまり **π 型ではなく「直列 L ＋ シャント C」の 2 素子**で、
アンテナ側の第 3 パッドは 1nF で GND に落としてある。

## この案件（#23）にとって何を意味するか

**#23 は一般論の「全層で 5〜10mm の禁止域」を指針にしてきた。**
**AN3216 を実際に量産している設計者が取っているのは、本体の縁から 1.30mm
（外形から 3.14mm）で、5mm ではない。**

| | 距離 |
|---|---|
| 一般論の指針 | 全層 5〜10mm |
| **Seeed の実装（AN3216・4 層）** | **アンテナ本体の縁から 1.30mm・全層同一** |
| いまの設計（出荷構成・直付け） | 本体基板まで **5.24mm**（`test_the_antenna_keeps_its_distance_from_the_main_board`） |

⚠️ **これは「5.24mm あるから安全」という結論ではない。**性質が違う:

- Seeed の 1.30mm は**同じ基板の中の、面内方向の**銅の逃げ。
  地板はアンテナの給電の一部として設計に織り込まれている
  （AN3216 のようなチップアンテナは地板を放射体として使う）
- #23 が問題にしているのは、**別の基板の大きな GND 面が、アンテナの
  斜め上に 5.24mm で覆いかぶさる**こと。これは Seeed が想定した
  「モジュールの外側は空いている」という前提を壊す側の話

**読みが変わるのはここ:** #23 の「上 4mm・下 1.6mm では、どう対策しても
指針 5〜10mm を満たせない」という記述は、**満たすべき基準を過大に見ていた
可能性がある。**Seeed 自身が 1.30mm で製品を出しているので、
**5mm を割ったこと自体は即座に不合格を意味しない。**

**それでも手 0 は要る。**基板の面内で銅を抜くことと、外部の金属面が
近づくことは別の物理で、机上のどちらの数字からも dB は出ない。
**#23 を閉じるのは実測だけ。**

## 副産物: モジュールの外側に何を置いてよいか

Seeed 自身は **アンテナ端の基板外形から 3.14mm を全層で空けている**が、
**基板はそこで終わっている**（外形 x=138.0236 で、アンテナは 0.271mm 内側）。
つまり **Seeed は「モジュールの外の空間」については何も保証していない。**
XIAO のデータシートが「金属で覆うな」としか書けないのはこのため。

**→ ケース側でアンテナの外側にどれだけ空けるべきかは、この資料からは決まらない。**
そこが手 0 で測る対象そのもの。
