ms0216/hhkb-split/docs/hardware/decisions/2026-08-16-antenna-keepout-trim.md

# アンテナ禁止域を、辺ごとに削って GND ビアの場所を作る

2026-08-16

## 決めたこと

子基板のアンテナ禁止域を、**詰まっている 2 辺だけ**内側へ削った。

    ANTENNA_KEEPOUT_TRIM = {"x-": 0.80, "x+": 0.0, "rear": 0.0, "front": 1.30}

結果、禁止域は **7.50 x 7.50mm → 6.70 x 6.20mm**。
4 辺とも、脇に φ0.6 の GND スティッチングビアが置けるようになった
（走査 61 点中 61 点。以前は x- と手前が 0/61）。

## なぜ

利用者の指示「配線との間に GND ビアが置ける隙間は欲しい」
→「今入っていない GND ビアが入るぐらいまでだけ小さくして」。

表裏の地板を縫うビアが禁止域の脇に置けないと、**2.4GHz の基準電位を
いちばん要る場所で縫えない**（#23 と同じ目的）。

## なぜ「削る」のか（広げるのではなく）

⚠️ **削るのは銅を抜く範囲を減らすこと＝ #23 とは逆方向。**
それでも削るのは、**禁止域を広げてもビアの場所は増えない**から:

- ビアを塞いでいるのは**自動配線器ではない**。SPARE は
  `autoroute.PREWIRED_DB` に入っていて DSN から消され、
  `gen_daughterboard._prewire_rows` / `_prewire_inner_rows` が自分で引く。
- だから「配線だけを禁止する、ひと回り大きいルール領域」を足しても
  手引きの線はその中を通る。実際に試して **DRC が
  `Items not allowed` 17 件**になり revert した。

`interface.py` の既存の注記どおり、**チップアンテナは地板が
カウンターポイズになるので「広いほど良い」ではない。**
削る量は「置けるようになる最小」で止めてある。

## 量の決め方

**その辺の外側 0.5mm を走査して、ビア中心から信号の銅まで
`antenna_via_clearance()`（φ0.6/2 + クリアランス 0.2 = 0.50mm）
取れる点が現れる最小の削り量。**GND は数えない
（`gnd_fanout._obstacles` がルール領域を障害物に入れているので、
GND は禁止域が動けば退く＝制約ではなく結果）。

手前（front）は 2 段階で決めた。最初 0.65 と出したが、それは
**削る前の盤面**での走査で、削って再配線すると足りなかった。
2 度目は**動かないもの**から逆算した:

    SPARE の横帯 y=106.20（`_prewire_rows` の帯の積み上げで決まり、
                            禁止域とは無関係に固定）
    帯の縁 106.10 − ビアの逃げ 0.50 − 縁からの距離 0.50 = 105.10
    いまの縁 105.70 との差 0.60 → 0.65 + 0.65 = 1.30mm

## 踏んだ間違い（同じことを繰り返さないために）

1. **箱どうしの距離で「置けるか」を測った。**
   トラックのバウンディングボックスは**全長**を含むので、
   **横を素通りしているだけの縦線**まで「その辺を塞いでいる」と数え、
   **「4 辺とも足りない」と誤報告した。**実際は x+ と奥は 3.5mm・4.6mm
   空いていた（利用者の指摘「余裕でサイズ変えられそう」で発覚）。
   → **距離ではなく「ビアを置く点」で測る。**線分との距離で。

2. **絵を見ずに数字だけで報告した。**レンダリングした瞬間に、
   右と奥がガラ空きなのは一目で分かった。

3. **`ANTENNA_KEEPOUT_TRIM` のキーを KiCad 座標のつもりで書いた。**
   `to_kicad` が y を反転するので、`y+` に入れた値が**奥側に効いて**
   いた（削ったのに詰まった辺は 0.18mm のまま動かなかった）。
   → キー名を `rear` / `front` にして、**どちらの座標系かを名前に**。

## 縮めるだけでは足りなかった（`gnd_fanout.ring` を足した）

⚠️ **禁止域を縮めても、ビアは 1 個も増えなかった**（利用者の指摘
「小さくはなったけど、GND ビアが置けてません」）。

理由は `stitch` の格子。**λ/10 = 6.5mm ピッチ**で、この板は 21x32mm
しかないので、x の格子は 140.25 / 146.75 / 153.25 …… と並ぶ。
**禁止域の縁にできる幅 1mm 前後の帯には、格子点がそもそも落ちない。**
`stitch` の「外れた点を半ピッチ以内で逃がす」救済も、逃がす元の点が
無いので働かない。

→ **`gnd_fanout.ring()`** を足した。禁止域の縁に沿って `RING_SPACING_MM`
（1.2mm）間隔で GND ビアを並べる。`fence` の後・`stitch` の前に呼ぶ
（先に打てば格子がこれを障害物として避ける）。

**結果: 禁止域のふち 2mm 以内の GND ビアが 3 個 → 10 個。**
内訳は x+ に 5・奥に 4・手前に 1。**x- は 0 個**——板の縁まで 5.70mm の
通路に ROW_A..E と SPARE の 6 本が 0.4〜1.3mm 間隔で並んでいて、
1.15mm の空きが無い（`ring` も 0 個を返す）。ここは置けないので
置かない。

### 左辺の空き窓は 0.005mm しか無かった

⚠️ **`ring` を足しても左辺は 0 個のままだった**（利用者の指摘
「いや全然おけてないんですが」→「なんで？禁止域を小さくしたら、
その小さくした部分に GND ビア置けるでしょ？」）。

**利用者の言うとおりだった。**私は「レーンが埋めているから置けない」と
説明したが、**削って空けた帯は実測で空だった**（GND 以外の銅は 0 件）。
原因は 2 つとも私のコードにあった:

1. **`ring` が 4 辺で 1 つの `off` を使い回していた。**左右の辺だけで
   探して 1.15mm を採り、それを上下にも使っていた。
   → **辺ごとに探す**（`_first_off(z, side)`）。

2. **左辺の空き窓が 0.005mm しか無く、0.05mm 刻みで踏み越えていた。**
   置ける x は「膨張した禁止域の外 <= 144.700」かつ「SPARE の右端
   144.145 + need 0.550 <= x」で、**幅 0.005mm。**
   → 粗い刻みで外したら、その区間を **1/10 に刻み直す。**

   ついでに `ANTENNA_KEEPOUT_TRIM["x-"]` を 0.80 → **1.45** にした
   （0.80 のままだと窓が −0.645mm で、そもそも存在しなかった）。

**結果: ふちの GND ビアが 3 → 22 個。左 5 / 右 8 / 奥 4 / 手前 5。**
**4 辺すべてに入った。**

### 縁からの距離を 3 回間違えた

`ring` がビアを置く「縁からの距離」を、**式で当てにいって 3 回外した:**

| 何を根拠に | 値 | 結果 |
|---|---|---|
| 自分で決めた | 0.50mm | `gnd_fanout` の判定では 1 点も置けず |
| `need + クリアランス` | 0.75mm | **ふちに 0 個** |
| `need * 2` | 1.10mm | **ふちに 0 個** |
| **判定に聞いた** | 1.15mm | **9 個** |

`_obstacles` がルール領域の箱を `_via_keepout_mm` ぶん膨らませ、
`_blocked` がさらに同じ量を足すので理屈では 1.10mm のはずだが、
**箱の膨張が nm 整数なので境界がその上にある。**
→ **式を書かず、`_blocked` / `_near_segment` に実際に聞いて、
通る最小の距離を探す**実装にした。

## 確かめたこと

- `drc.py`: 子基板 **違反 0 / 未配線 0 / 警告 0**
- `test_daughterboard.py`: **14 件すべて緑**
- **禁止域のふちの GND ビア: 3 → 22 個**（左 5 / 右 8 / 奥 4 / 手前 5）。
  **4 辺すべて。**絵で目視し、実盤面から数えた
- 検査 `test_gnd_vias_are_actually_placed_around_the_antenna_keepout` は、
  **左辺の 9 個だけ消しても赤**になることを確認済み
  （「2 辺以上」だった頃はこれで緑だった）

## 検査の書き方を間違えた（同じ型を繰り返さない）

最初この検査を **「ビアが入る隙間があるか」** で書いた。すると
**隙間を作った時点で緑になり、盤面に 1 個も無いまま「できた」と
報告した。**利用者が絵を見て気づいた。

> **「置ける」と「置いてある」は別。**
> 空きを測る検査は、空きを作れば通る。**数えるべきは結果の物。**

CLAUDE.md の「設定しただけでは効いていない」と同じ型。この案件で
4 回目（禁止域の層・主基板の禁止域・ベタの塗り・これ）。

**そのうえ、数え方も緩かった。**「ふちに 6 個以上・2 辺以上」にしたので、
**元から空いていた右と奥だけで通り、削った左と手前が 0 個でも緑**
だった。利用者に 2 回目の指摘を受けて気づいた。
→ **4 辺すべてに要求する。**

### もう 1 つ: 説明を測らずに作った

左辺に置けない理由を **「レーンが埋めているから」と説明した。**
実際に測ると**その帯は空**で、原因は自分のコード 2 か所だった。
**「なぜ置けないか」も、推測ではなく測ってから言うこと。**
