ms0216/hhkb-split/docs/hardware/decisions/2026-08-07-four-layer.md

# 本体基板は 4 層にする

**日付**: 2026-08-07
**状態**: ❌ **2026-08-12 に 2 層へ確定・撤回済み。この文書の第 1〜5 節は
もう採用されていない（下の「先に読むこと」を参照）。**

---

## ✅ 先に読むこと（2026-08-13 追記・決着）

**本体基板は 2 層で確定した。**`tools/gen_pcb.py` が
`board.SetCopperLayerCount(2)` を呼んでおり、`pytest tools/test_pcb.py`
の `test_the_main_board_is_two_layers_with_ground_poured_on_both` が
層構成（F.Cu・B.Cu の 2 層）と、両面に GND ベタが実際に塗られている
ことを恒久的に検査している。DRC は左右とも違反 0・未配線 0（実測、
基板ハッシュ一致で確認済み）。

以下は 2026-08-12 時点の再検討の記録（結論に至る過程）。

**この文書の「2 層では通らない」は手書きルータ時代の話で、いまの基板の
実態と違う。この文書を根拠に 2 層化を却下しないこと。**

下の第 1 節は「行の引き回しが 1.65mm の通路に入らない」と書いているが、
その後 **Freerouting に切り替えたときに配線をやり直しており、第 2 節の
層の割り当て（L1＝列のバス、L3＝行の引き回し）は実装されなかった。**

実際に出来ている基板を数えるとこうなっている（左基板・実測）。

| 層 | 中身 |
|---|---|
| **F.Cu** | **ビアのランドだけ。配線 0 本**（＝**丸ごと空いている**） |
| **In1.Cu** | GND ベタのみ。配線 0 本 |
| **In2.Cu** | 配線 80 本 |
| **B.Cu** | 配線 185 本 |

**信号は 2 層（In2.Cu と B.Cu）に収まっている。**「2 層では入らない」は
根拠になっていない——それどころか、**すでに 2 層に収まっていることが
実測で示されている。**

**この文書が実態に追いつかないまま残っていた**こと自体が問題だった。
CLAUDE.md の「節を直しても一覧を直さない」と同じ型。

当時の未検証点（GND ベタの分断をスティッチングビアで繋ぎ直せるか）は、
指摘 4・5 の対応で解消した。浮いた GND を 0 個にし、斜めのバスにも
ビアを通した（コミット `84df0cb`・`86e0101`）。DRC 0 件で確認済み。

---

## 1. なぜ決める必要が生じたか

74HC595 とケーブルコネクタを載せて配線しようとして、**2 層では通らない**
ことが分かった。

現在の 2 層の使い分けはこうなっている。

| 層 | 使途 | 空き |
|---|---|---|
| **B.Cu（裏）** | ソケット→ダイオード、**行のバス（水平）** | ソケットとバスでほぼ埋まる |
| **F.Cu（表）** | **列のバス（垂直）** | キー中心 +2.2〜6.0mm の帯だけが通り道 |

ここへ「ケーブルから 5 本の行へ降ろす配線」を足す必要がある。

- 行のバスは裏面を水平に走るので、**5 本の行すべてより外側**を縦に抜けるしかない
- その通路の幅は **1.65mm**

```
PCB 左端 → 最左キー中心          10.65mm
最左キーのソケットが占める範囲    1.65 .. 18.45mm
                                  ↑ 縦に抜けられるのはここまで
```

0.2mm の配線と 0.2mm の隙間で 5 本並べると 1.8mm。**入らない。**
表面へ逃がそうにも、列のバスが通り道を使い切っている。

**これは配線の工夫で解ける問題ではなく、層が足りていない。**

---

## 2. 4 層にする

| 層 | 用途 |
|---|---|
| **L1 (F.Cu)** | 列のバス、信号 |
| **L2** | **GND ベタ（全面）** |
| **L3** | 電源（3V3）＋ 行の引き回し |
| **L4 (B.Cu)** | ソケット、ダイオード、行のバス、部品 |

行の引き回しを L3 へ逃がせば、通路の問題は消える。

### 副次的だが、こちらの方が効くかもしれない

利用者が挙げた品質の条件に「**回路の綺麗さ・ノイズ耐性**」がある。
4 層の GND ベタは、そこに直接効く。

| | 2 層 | 4 層 |
|---|---|---|
| GND | 部品を避けた歯抜けのベタ | **全面の連続した面** |
| 戻り電流の経路 | 遠回りすることがある | 信号の真下を通る |
| BLE 2.4GHz の基準電位 | 場所によって揺れる | 安定 |
| 電源のインピーダンス | 配線の細さで決まる | 面なので低い |

分割キーボードは **2.4GHz の無線を 2 台、至近距離で動かす**。
基準電位が安定していることの価値は、ここでは特に大きい。

---

## 3. 費用

JLCPCB の 5 枚枠で比較する（概算）。

| | 2 層 | 4 層 |
|---|---|---|
| 基板代 | 約 2 ドル | 約 7 ドル |

**差は 5 ドル程度。** 送料と PCBA の費用に比べれば誤差の範囲で、
配線が通らないという問題と、ノイズ耐性の向上に見合う。

---

## 4. 検討して捨てた案

| 案 | 捨てた理由 |
|---|---|
| 行のバスを基板の周囲に迂回させる | 通路が 1.65mm しかないのは変わらない |
| 列のバスの帯を狭めて表面に行を通す | 帯はスタビライザー穴に挟まれた唯一の空き。これ以上は取れない |
| ケーブルを左右に分けて 2 本にする | 部品が増え、行の通路の問題は解けない |
| キー配列を詰めて空きを作る | **HHKB 再現という基本方針を捨てることになる。却下** |

---

## 5. ~~やること~~（❌ 撤回済み。2 層に確定したので、この節は実行しないこと）

1. ~~`tools/gen_pcb.py` を 4 層対応にする（`SetCopperLayerCount(4)`）~~
2. L2 に GND ベタ、L3 に 3V3 ベタ＋行の引き回し
3. 74HC595・受動部品・FFC コネクタを裏面の奥の帯に置く
4. 電源部（スライドスイッチ・電池線・ショットキー・分圧）を置く
   — **ケース内寸が決まってから**（スイッチに手が届く位置である必要がある）
5. DRC 0 件を確認

子基板は 2 層でよい（部品が少ない）。
