ms0216/hhkb-split/docs/hardware/decisions/2026-08-07-keyscan.md

# キースキャン方式: チャープレックスを破棄し、74HC595 マトリクスへ

**決定日: 2026-08-07 ／ 状態: 確定（基板発注前）**

## 決めたこと

キースキャンを **チャープレックス（`zmk,kscan-gpio-charlieplex`）から
「行×列マトリクス ＋ キーごとにダイオード 1 個」＋ シフトレジスタ 74HC595
（`zmk,kscan-gpio-matrix` ＋ `zmk,gpio-595`）へ変更する。**

チャープレックスへ戻すことは禁止する。`tools/test_keyscan.py` が機械的に止める。

## なぜチャープレックスを選んでいたか

Seeed XIAO nRF52840 を使うのは**技適（211-220207）を取得しているから**で、
これは動かせない制約。その XIAO で使える GPIO は D0〜D10 の 11 本しかない。

一方、右半分は 34 キーある。普通のマトリクスで 34 キーを読むには
最低でも 12 本必要（6 行 × 6 列、または 5 行 × 7 列）。**1 本足りない。**

チャープレックスなら 7 本で 42 箇所を区別できるので、この制約を回避できる。
ここまでの筋道は正しかった。**破棄の理由になったリスクを検証しないまま
先へ進めていたのが誤り。**

## 破棄の理由 1: 2 キー同時押しでゴーストが出る

チャープレックスには行と列の区別がなく、どのピンも出力にも入力にもなる。
そのため「ピン i から k へ流れるキー」と「k から j へ流れるキー」を同時に
押すと、**i → k → j と電流が通り抜けて、押していない「i から j へのキー」が
押されたと誤検出される**。

普通のマトリクスならダイオードがこの抜け道を止めるが、チャープレックスでは
**抜け道の途中のダイオードも順方向**なので止まらない。頼れるのは
「ダイオード 2 個ぶんの電圧降下で LOW と判定させる」ことだけになる。

nRF52840 の入力閾値は **VIH = VDD × 0.7、VIL = VDD × 0.3**
（[Nordic のデータシート](https://infocenter.nordicsemi.com/topic/com.nordic.infocenter.nrf52832.ps.v1.1/gpio.html)）。
3.3V 動作で計算すると:

| 条件 | 必要なダイオード順方向電圧 Vf |
|---|---|
| 本物のキー（ダイオード 1 個）を HIGH と読ませる | 3.3 − Vf ≧ 2.31 → **Vf ≦ 0.99V** |
| ゴースト（ダイオード 2 個）を LOW と読ませる | 3.3 − 2Vf ≦ 0.99 → **Vf ≧ 1.155V** |

**両立しない。** どんなダイオードを選んでも解決できない。実際には抜け道の
電圧は HIGH でも LOW でもない未定義帯（0.99〜2.31V）に落ちるので、
**動くかどうかが部品のばらつきと温度に左右される。**

さらに悪いことに、**この設計は単3電池 2 本で動く**。電池は 3.0V から 2.0V まで
下がり、閾値は VDD に比例して動くのにダイオードの電圧降下はほぼ一定なので、
**成立条件が電池残量とともに動く**。「新品のうちは動くが、減ってくると誤爆する」
という最悪の壊れ方をしうる。

HHKB の使い勝手では Shift・Ctrl・Fn との同時押しを常用する。ここが不安定な
キーボードは、この計画の目的そのものを満たさない。

参考: [Keyboard Builders' Digest — Square or round-robin matrix](https://kbd.news/Square-or-round-robin-matrix-1400.html)
（「ゴーストを避けるには部品を非常に慎重に選ぶ必要がある」「完全に問題なく
動くなら QMK にとっくに入っているはず」）

## 破棄の理由 2: 常時スキャンで電池が持たない

ZMK のメンテナ自身が「**無線機には使わないほうがいい。この方式は常時スキャンを
強いるため電池寿命に重大な影響がある**」と述べている（上記記事より）。

ZMK のチャープレックスドライバは `interrupt-gpios` を指定しない限り
`poll-period-ms`（既定 1ms）で永久にスキャンし続ける。**乾電池駆動という
基本方針と真っ向から衝突する。**

## 採った方式

ZMK 公式が「**標準マトリクスでキー数に対してピンが足りない場合の推奨手段**」と
明記している 74HC595 シフトレジスタを使う
（[Configuring Shift Registers](https://zmk.dev/docs/development/hardware-integration/shift-registers)）。
「消費電力が非常に小さく、かつ安価」であることが推奨理由として挙げられている。

### ピン割り当て（XIAO nRF52840 / D0〜D10 の 11 本）

| ピン | 用途 |
|---|---|
| D0 | 電池電圧の測定（ADC が使えるのは D0〜D5 だけ） |
| D1〜D4, D9 | 行 5 本。**MCU 直結の入力**（⚠️ 当初は D1〜D5。ROW4 は後に D9 へ移した——[open-gaps #23](../open-gaps.md) の D9 移設。MISO は読まないので psels から外して解放。出所: `hhkb_split.dtsi`） |
| D5 / D6 | 予備 |
| D7 | シフトレジスタの CS（ラッチ） |
| D8 / D10 | SPI（SCK / MOSI）。MISO（D9）は上記のとおり行に転用 |

ZMK の公式サンプルは CS に D9（MISO）を充てているが、xiao_ble の pinctrl は
P1.14 を MISO として確保しているため競合しうる。こちらは D7 を CS にした。

**行を MCU 直結にしているのは公式の指示による。** 入力が MCU のピンなら
割り込みで起こせるので、常時スキャンせずに済み電池が持つ。シフトレジスタは
列（出力）側にだけ使う。理由 2 がここで解消する。

### 行列の構成

> ⚠️ **訂正（基板を起こしたときに変更）: 右は 9 列・595 は 2 個。**
> 下の「`` ` `` を row4, col3 へ回して 8 列に収める」案は廃止した。物理的に
> 最上段のキーを論理最下段に置くと **90mm の配線が 4 段ぶんのスイッチを
> 横切り**、DRC が交差と短絡として検出した。部品 1 個（約 30 円）を足して
> 2 個を数珠つなぎにする方が配線が素直。出所: `tools/circuit.py`（右は
> U1＋U2）・`hhkb_split_right.overlay`（ngpios = 16）・`hhkb_split.dtsi` 冒頭。

| | 行 | 列 | 収容数 | 実キー数 |
|---|---|---|---|---|
| 左 | 5 | 6 | 30 | 27 |
| 右 | 5 | **9** | 45 | 34 |

行と列は物理配列そのまま。~~ただし右半分の最上段だけは 9 キーあり 8 列に
収まらないので、`` ` ``（バッククォート）1 つだけを最下段の空き（row4, col3）へ
回した。これで右も 8 列に収まり、左右とも 74HC595 は 1 個で足りる
（数珠つなぎ不要、部品構成も同一）。配線は基板の右端を縦に 1 本通すだけ。~~
（↑上の訂正のとおり廃止）

### 併せて直したこと

分割の書き方も直した。左右で別々の `matrix-transform` を定義していたが、
これは非標準で右半分のキー位置がずれる恐れがあった。corne など ZMK 公式
シールドにならい、**1 つの transform を左右で共有し、右半分には
`col-offset = <6>` を足す**形にした。

## 代償

シフトレジスタが増える（左 1 個・右 2 個。1 個 30 円程度。品番はのちに
SN74LVC595APWR へ変更——動作電圧の下限）。JLCPCB の実装対象なので
組み立ての手間は増えない。

## 影響

- **フェーズ D（基板設計）はこの構成で進める。** ダイオードは 61 個（キーごとに 1 個）
- **Task C2 の内容が変わった。** チャープレックスの配線対応を実測する作業は
  不要になり、代わりにマトリクスの疎通とゴースト試験を行う
  → [task-c2-keyscan.md](../task-c2-keyscan.md)
- `docs/superpowers/plans/2026-08-05-phaseC-electrical-firmware-validation.md` の
  Task 2 と Task 3 はこの決定で置き換わった

## 教訓

**方式を選ぶときは「動くか」だけでなく「その方式が一般的でない理由」を調べる。**
チャープレックスが ZMK にありながら採用例が少なく、QMK が今も対応していない
ことには理由があった。ピン数の制約という「解きたい問題」に合う解を見つけた
時点で満足し、その解の代償を調べていなかった。

この見落としは、利用者から「この方式は一般的なのか、実用に耐えるのか」と
問われて初めて調べ直したことで見つかった。**基板を発注していたら
41 キーぶんの配線が無駄になっていた。**
