ms0216/hhkb-split/docs/hardware/decisions/2026-09-05-case-redesign-plan-a.md

# 2026-09-05 筐体の作り直し（案 A: 二枚貝の上シェル ＋ 奥板）

利用者の指示（2026-09-05）: 「組み立て性・見栄え・頑丈さ・印刷のしやすさなど
可能な限り多くの視点で、最も良い筐体にゼロから作り直す。子基板と左基板は
発注済みなので、その変更が要る修正はできない。過去の制約が障壁なら言え、
取捨選択する」。ブランチ `explore/flatten-bump-lid` で作業。

## 優先順位（利用者）

1. **HHKB 実機の使い勝手の再現**（最優先・CLAUDE.md と同じ）
2. 組み立て性・見栄え・頑丈さ・印刷のしやすさは**同格**。ぶつかる場面ごとに選ぶ

## 外した過去の決定（利用者が選んだ）

| 決定 | 外した理由 |
|---|---|
| 上ケースは「ケースと同一外形の落とし込み蓋」（2026-08-07） | 平面方向の逃げ 0 で奥の留めが原理的に作れなかった（#12） |
| 電池蓋はスライド＋ビード 0.4（2026-08-12） | 3 度作り直し・薄肉補修 4 回・開けるのに 14.7N |
| コブ 18mm を「受け入れた差」で凍結 | 根拠が保守値の連鎖。測り直して縮める |

**維持**: XIAO のピンソケット（#27・`DB_XIAO_LIFT` 10.5）、底面にネジ無し・
振動吸収シート、電源スイッチ SS12D01G4-G を奥壁の溝に落とし込み、
A1 mini 幅（左 144.4 / 右 177.7）、傾斜 7.3°・手前 17.5・本体奥行 108。

## 新しい事実（データシート BH-325-1A・図面 3251A-0410）

- 109.0±1.0 × 16.6±0.5 × 16.8±0.5。**電池は上面（長辺の開口）から入れる樋型**
  → 奥から出し入れするには箱を横倒しにして開口を奥へ向ける
- **床に φ2.4 の取付穴 2 個**（内側から φ3.8×0.8 の座ぐり）→ M2 で締められる。
  「囲うだけ」（旧 HELD_BY）は部品側に固定手段があるのに使っていなかった
- ソケット板下 1.80（PG151101S11）、MX のプレート〜基板 3.5 は Cherry 規格そのもの。
  箱は基板の下に潜らないので、コブ深さに効くのは奥の余白と壁だけ

## 構成

| 部品 | 役割 | 印刷の向き |
|---|---|---|
| 下シェル `case` | 床・側壁・奥壁（SW 溝・USB-C・LED 窓）・電池室・子基板ボス・底面造作 | 床を下 |
| 上シェル `topcase` | ベゼル面＋コブ天井（**一枚の 7.3° 面**）＋スカート（手前・左右） | **ベゼル面を下**（平面なので段差ゼロ） |
| 奥板 `rear_plate` | 電池窓（109 幅）を塞ぐ板。上縁は上シェルの天井の下（2026-09-06 にリップと足を廃止）。下縁の舌（内側の肉 0.8・深さ 1.0・外面に 0.3 の逃げ）が床の溝に入る。外すときは板の上縁の切り欠き（15 × 2.5・天井の奥縁の下に隠れる）に爪を掛け、舌の外下の角を支点に 15° まで倒し、持ち上げて舌を抜く | **内面を下**（舌がベッドに着く。旧 L 字の足は溝の部分が浮いて刷れなかった） |
| プレート・脚・ゴム足・ナット | 現行どおり | |

- 側面の合わせ目: **リム面と平行・リムの 3.0 下**（`SKIRT_LAP`。2026-09-06 に
  水平から変更。利用者「はめ合わせはプレートの厚み分で足りるのでは」→ 位置決め
  と目隠しだけなので高さは要らない。水平だと奥で 14mm の薄い壁 2 枚と 14mm の
  こすり合わせになっていた。手前では 9.4 → 6.4）。相欠きの帯は
  **下シェルの帯 1.2（内）＋上シェルのスカート 1.2（外）**、隙間 0
  （`SKIRT_FIT`・利用者の判断「隙間はガタになる。合わなければ削る」）。
  ⚠️ 最初は側壁ごと上シェルに持たせたが、プレートを受ける段と押さえる縁が
  同じ部品に入って**プレートが入らなかった**（利用者が .blend で発見）。
  受けるのは下・押さえるのは上に戻した。ベゼルの開口の隙間は 0.9 → 0.725
  で枠 2.4（6 周）・押さえ 1.2（3 周）。**手前壁は相欠きにしない**——手前の
  ネジボスが外面に接していて、外側を削ると熱圧入インサートが露出する
  （箱モードの検査が 0.19mm³ で捕まえた）。手前はリム面で突き合わせ。
  **外形幅は不変**
- 実機再現（dimensions.md §4）: 上下シェルの合わせ目（3）は再現。**手前面の
  傾き 12°・上縁 R6（1・2）は再現できない**（2026-09-05 に数字で確認）:
  手前の M2 ボスが外面から 0.74 はみ出す位置にあり、内側の端は基板の手前縁まで
  0.44。面を傾けるとボスが削れてインサートが露出する。基板は発注済み。
  ベゼルのバーの範囲だけ 12° に倒すと下端に幅 1.2 の段ができ、実機に無い線が
  増えるので入れない（`FRONT_FACET_H = 0`）。上縁 R2 は OCC のフィレットが
  **通った結果が奥の天井の一部を黙って失っていた**（max Z 33.53→33.26）ので
  入れない（`FRONT_EDGE_R = 0`）。丸めは試作後に手やすりで。底縁 R1.5（4 の
  代用）は入れた（削れた体積 257 ≈ 見積り 260 で健全）。手前端 17.5 は不変
- 奥の隅: 上シェルの側壁が角の丸みを回って奥面の接線まで続く（2026-09-06。利用者
  「縦の継ぎ目を手前・左右から見せたくない」。以前は奥面から 6 の柱を下シェルが
  持ち、側面に縦の継ぎ目が出ていた）。縦の継ぎ目は奥面の角の接線上、隙間 0.1
- 奥: スカート無し。上シェルの奥縁は奥壁の上に突き合わせ、天井は奥面まで通す。
  奥板はその下に立つ（2026-09-06。リップは押さえになっておらず、座ぐりは裏返して
  刷ると宙に出た）
- 電池箱: 横倒し（開口が奥）、仕切り壁へ M2×2。コブ深さは再導出しても 17.8 で
  **18 のまま**（箱は基板の下に潜らないので、効くのは奥の余白 1.0 と壁 2.4 だけ）
- 奥板: M2×2 を奥壁のボスへ水平に。ビード・庇・舌・スライドは全廃
- 隙間: スカート **0**（`SKIRT_FIT`・上記）／ 奥板 0.3［未実測・クーポン先行］

## 留め（HELD_BY の新版）

上シェル = 手前 M2×3 ＋ スカート（位置決め）＋ 奥面 3 本目。奥板 = M2×2（上シェルの桟へ）。
電池箱 = M2×2。電源 SW = 溝＋奥リブ＋**上シェル奥縁の裏面が上への抜けを塞ぐ**。
プレート = 下シェルの手前壁と側壁の帯（リム面）が受け、上シェルのベゼルの縁が
押さえる（4 辺。光線走査で確認: 左右 25/25・奥 34/34・手前 31/34、無い 3 点は
ネジ穴）＋手前共締め。**奥端は下シェルの電池の仕切り壁**（リム面まで伸ばした・厚み
2.0・**外壁から子基板の場所の手前まで**。利用者「受けになったので可能な限り伸ばす」）
が受ける。上シェルの棚は裏返して刷ると空中の庇になり印刷が壊れたので廃止
（利用者の試し刷り 2026-09-06）。上シェルは奥のバーで奥行方向の位置を決めるだけ。
壁の両端（箱の端）の 4×4 の切り欠きは箱の両端から出るリード線を基板側へ通す逃げ。

## 組み立て順（INSERT_PATH）

① 電池箱を奥の窓から（仕切り壁へ M2×2） ② 子基板を手前から入れて上へ
③ **上シェルを裏返し、プレート＋基板を真っ直ぐ落とす**（奥のバーが奥縁を止め、
**上シェルから下向きの手前のピン**がプレートの切り欠きに入って位置を決める。
2026-09-06 に上シェルの棚と溝を廃止したので傾けない） ④ その組を下シェルに
被せる（ピンが下シェルのボスの穴へ 2.6 入り、**電池の仕切り壁**の上面が
プレートの奥端を受ける） ⑤ 裏から M2×3 ⑥ 奥板 M2×2、奥面 3 本目。
斜め差し・撓ませる操作は無し。

## 頑丈さ・ズレ止め（2026-09-05・利用者「見えない所ならネジを増やしてよい」）

- **手前 M2×3 のボス**: 円柱 φ5.6・中心 51.5 ではインサート（外径 3.2）の外側の
  肉が 0.46 で、圧入で割れる。基板の手前縁（平面図 48.31）が動かせないので、
  ボスを**壁と一体の角柱**にして内端を基板の縁 + 0.2 で止め、インサートを
  内へ寄せた（`MOUNT_Y` 50.91 → **51.16**・2026-09-06 根元の強化）。肉は内側 1.05 /
  外側 1.24（上シェルのバーは開口の縁が傾くので上端で薄い。STL 実測 1.18 / 1.22）。ベゼルの座ぐりが
  外面を 0.14 破っていた問題も消えた。捕まえナット案は「工具を増やしたくない」
  で見送り（実際は工具不要だが、部品が増える）
- **奥面 3 本目の M2**: 奥板のリップは電池窓の幅（109）しか押さえない。子基板側
  （x = 子基板中心 − 8、z ≈ 27）で奥壁を貫き、上シェルの天井裏のボスへ
- **開口を 7.3° に傾けて切る**: 垂直に切っていた開口は、キャップの面と 7.3°
  ずれ、手前段では隙間 0.9 の時点で縁まで 0.18 しか無かった（0.725 で接触・
  箱モードが 0.03mm³ で検出）。プレートと同じ姿勢で切り、全段で隙間 0.725
  （見え 1.05）。最下段の覆いも同じ姿勢。`plate_placement` を gen_case へ移した

## 試し刷り 1 回目の指摘（2026-09-06・利用者）と対応

| 指摘 | 対応 |
|---|---|
| 手前のネジが表に見える | **裏から**に変更。底に頭の座ぐり（頭は底面より 0.2 沈む＝シートで覆える。9/5 の「底は平ら」はこれで満たす）、ボス柱は M2 のバカ穴、雌ねじは上シェルのベゼル手前バーの裏のインサート（座 = プレート上面 + 0.4、下穴はインサートより 1.0 深い）。M2×14 |
| 電池のネジ受け・スイッチの受けが浮いていてサポートが要る | 両方とも床から立てた |
| 開口の角が痛い | 開口と最下段の覆いの上縁を 0.8 の面取り（丸めはカーネルが不安定）。手前の縁は表の座ぐりが 0.36 に迫っていて失敗したが、ネジを裏へ移して解消 |
| 仕切り壁が箱のケーブル受けに当たる | 利用者の実測（黒線側の端から 14 / 53.5 / 93、幅 4、高さ 5.5）の位置だけ 5.5 に切り下げ、他はリム面まで |
| 箱がリード線の分ずれる（2.0） | 箱を外壁から 2.0（`BATT_WIRE_ROOM`。利用者「安全側で 2.0」）。左の電源スイッチの帯は 6.76 になり、受け箱の両脇の逃げ 0.2 → 0.1、奥板の掛かり代 2.0 → 1.5、窪みは空きの中へ寄せて 3.96（利用者が 3.3〜3.8 を許容）。**スロットの電池側 0.19 が窪みの外**（壁 2.4 のまま。ツマミの出は 1.6）。⚠️ 箱の長辺は図面 109±1.0 で、現物が長いと受け箱が入らない——**実測待ち（BATT_X）** |
| USB-C の穴が大きく四角い | 樹脂用の座ぐり（12.4×7.4）を廃止（メスの面は外面より 0.26 外で、樹脂は壁に入らない）。穴はメス断面 + 0.4 の角丸 r1.2（両端半円だとメスの角が出る） |

## 電池交換の工具なし化は見送り（2026-09-05・利用者）

候補は磁石（φ4×2 ×4）／撓む爪（腕 20mm・ひずみ 0.27%）／回す止め具。
利用者「電池を変える頻度は非常に少ないので、ねじでもいい」。奥板は M2×2 のまま。

## 奥の棚の剛性（計算・2026-09-05）

利用者の懸念「上辺の受けは撓み防止のためだったはず」への答え。荷重はキーを
底まで押し切る 1〜2 N（キー 60 gf ＋ 底打ち）。
- 棚を吊るベゼル奥のバー（5.65 × 6.6、長さ 140）だけで I ≈ 135 mm⁴、中央 2 N で
  δ = FL³/(48EI) ≈ 0.24 mm（E = 3.5 GPa 文献値。FDM は 2 GPa 程度で最悪 2 倍）。
  実際は天井板・スカート・桟・奥板が繋がるのでこれより小さい
- 旧（天井から垂らしたフランジ 2.4 × 11）: 同じ式で ≈ 0.12 mm。同じ桁
- 受け無し（2026-08-29 の状態、プレート 1.5 の片持ち 100 mm）: ≈ 4.9 mm
→ 受けとしては足りる。試し刷りで指で押して確かめる。

## 新しい検査

- 奥板の上縁が天井の下にある（0.3 上げると当たる）／上シェルは上へ抜ける／奥板は舌を支点に 5/10/15° 倒し・持ち上げ・引き出しで両シェルに当たらない（gen_assembly.rear_plate_path）
- 電池箱のネジ軸線上に奥の窓からドライバー φ6 が通る
- スカートと外壁の重なりが全周 3.0（`test_the_skirt_lap_is_uniform`）・外形幅が 144.4 / 177.7 を超えない
- 上シェルの見せ面（ベゼル面）が一平面（印刷向きの前提）

## 実装の順（1 段ずつ箱モードで当たりを見る）

1. 下シェル: 奥面の蓋機構を撤去 → 電池箱を横倒しへ → 仕切り壁を高くしボスを
   立てる → 奥の窓＋奥板ボス → 外壁上部の削り → 底縁 R
2. 奥板 `build_rear_plate`
3. 上シェル: 落とし込みをやめスカートへ → コブ天井を上シェルへ移す → 手前面
4. gen_assembly / envelopes / interface / 検査の更新、古い定数と STL を消す
5. `refresh_view.sh` → `pytest tools` → 実形状
