ms0216/hhkb-split/tools/autoroute.py

"""未配線の基板を Freerouting に通して配線する。

**手書きのルータをやめた理由**は
docs/superpowers/specs/2026-08-08-pcb-autoroute-design.md にある。
要点は、衝突判定を持たないルータは任意のネット対を短絡させ、
それは経路の調整では 0 にならないということ。

    "$KPY" tools/gen_pcb.py --no-route   # 未配線の基板を出す
    "$KPY" tools/autoroute.py            # 配線する
    .venv/bin/python3 tools/drc.py       # 確かめる

DSN が層構成・クリアランス規則・NPTH の keepout・GND ベタ（面として）を
運ぶことは実測で確認済み。
"""

import json
import os
import re
import shutil
import subprocess
import sys
from pathlib import Path

import pcbnew

import boardhash
import gnd_fanout
from gen_pcb import replay_matrix

ROOT = Path(__file__).resolve().parent.parent
PCB = ROOT / "pcb"
UNROUTED = PCB / "unrouted"
HALVES = ("left", "right")             # マトリクスを持つ基板
# **配線する基板は 3 枚。**子基板は 2026-08-14 に手配線をやめて
# ここへ来た（open-gaps #41）。部品が 9 個に増えて、衝突判定を持たない
# 手書きルータでは DRC が収束しなくなったため。
BOARDS = HALVES + ("daughterboard",)
PASSES = 300      # 800 に増やしても未配線は減らなかった（2026-08-13）

# **配線は B.Cu を主にして、交差だけ F.Cu の短い橋で越える**
# （2026-08-15・利用者「B.Cu で引き、交差はビアで最短だけ F.Cu に潜る」）。
#
# ⚠️ **2026-08-14 の「autoroute_settings を足すな」という注記は誤りだった。**
# 当時 `(via_costs N)` + `(start_ripup_costs 100)` を「structure の末尾」に
# 入れたつもりで左が未配線 66 本に激増し、値を変えても同じだったので
# 「ブロックの存在そのものが悪い」と結論していた。**そうではない。**
# 2026-08-15 に jar を展開して構文を読み直したところ:
#
#   1. **挿入位置が parser スコープの中だった。**`"\n  )\n"` を正規表現で
#      探すと structure ではなく **parser の閉じ括弧に当たる**（実測）。
#      未知のスコープは黙って捨てられるので、**値を変えても何も起きない。**
#      「値ではなくブロックの存在が効く」の正体はこれ。
#      → **括弧を数えて structure の終わりを求める**（_autoroute_settings）。
#   2. **層ごとのコストは `(layer_rule <層名> ...)` の中**にある。
#      当時は global の via_costs しか書いておらず、**層コストは
#      一度も設定されていなかった。**
#
# 構文は Freerouting 2.3.0 の io/specctra/parser/AutorouteSettings.class を
# 逆アセンブルして確認した（推測ではない）。
#
# **効くのは via_costs で、trace の層コストではない**（実測）。
# 層コスト比を 5 / 20 / 100 と振っても F.Cu は 22.1% で全く動かない。
# 一方 via_costs を下げると F.Cu が減る——**B.Cu に留まるにはビアを
# 惜しまず打つ必要がある**ので、ビアが高いと長い F.Cu の迂回を選ぶ。
#
#     via_costs   左 F.Cu   右 F.Cu   右ビア
#        30        22.1%      —         —
#        15        23.2%      —         —
#         8        19.5%      —         —
#         6         —        19.2%      81
#         5        15.0%     19.5%      90
#         4         —        20.9%      87
#         3        16.0%      —         —
#       **2**    **14.6%** **16.8%**   103   ← いまここ（左右とも最良）
#         1        16.8%      —         —
#         0        16.8%     24.8%     119   ← **最悪。元に逆戻り**
#
# ⚠️ **0 にしてはいけない**（2026-08-15 に実測。利用者の問い
# 「ビアコストは 0 とか最小にできないのか」）。**F.Cu が増える。**
# 右では 24.8% と、何もしない状態（25.1%）へほぼ逆戻りした。
#
# **ビアが無料だと「橋を短くする理由」が消えるため。**3 回潜って戻る
# 経路も 1 回で済む経路も同じ値段なので、ルータは経済性を考えるのを
# やめてふらつく。ビアは増える（119 個）のに F.Cu も増えるという、
# 両方損をする状態になる。
#
# **「短い F.Cu は歓迎、長い F.Cu は嫌う」を実現しているのは、
# ビアにわずかな値段が付いていること。**橋が短いほどビア 2 個分の
# 元が取れるので短い橋が勝ち、長い F.Cu は「そんなに走るなら
# 潜り直せ」と負ける。0 にするとこの選別が効かなくなる。
#
# 値は単調ではない（4 → 5 → 6 が行ったり来たりする）。コストを変えると
# 探索経路ごと変わるため。**1〜2 ポイントの差で良否を決めない。**
VIA_COSTS = 2          # 左右とも最良。0 は逆効果（上の表）
PLANE_VIA_COSTS = 5
START_RIPUP_COSTS = 100
# 層コストは効かないが、**意図を DSN に残す意味で B.Cu を安くしておく**。
LAYER_TRACE_COSTS = {"F.Cu": 100, "B.Cu": 1}


def _autoroute_settings(dsn):
    """B.Cu を主層にするコストを DSN の structure スコープに入れる。

    ⚠️ **正規表現で閉じ括弧を探さないこと。**`"\\n  )\\n"` は parser
    スコープの閉じに先に当たる。そこへ入れると未知スコープとして
    黙って捨てられ、**何の効果も無いのに「入れた」と思い込む**
    （2026-08-14 の誤結論の原因）。**括弧を数える。**
    """
    t = dsn.read_text()
    i = t.index("(structure")
    depth = 0
    for j in range(i, len(t)):
        if t[j] == "(":
            depth += 1
        elif t[j] == ")":
            depth -= 1
            if depth == 0:
                break
    else:
        raise SystemExit(f"{dsn.name}: structure スコープが閉じていない")

    rules = "".join(
        f"    (layer_rule {layer}\n"
        f"      (active on)\n"
        f"      (preferred_direction horizontal)\n"
        f"      (preferred_direction_trace_costs {cost})\n"
        f"      (against_preferred_direction_trace_costs {cost})\n"
        f"    )\n"
        for layer, cost in LAYER_TRACE_COSTS.items())
    block = ("\n  (autoroute_settings\n"
             "    (fanout off)\n    (autoroute on)\n    (postroute on)\n"
             "    (vias on)\n"
             f"    (via_costs {VIA_COSTS})\n"
             f"    (plane_via_costs {PLANE_VIA_COSTS})\n"
             f"    (start_ripup_costs {START_RIPUP_COSTS})\n"
             f"{rules}"
             "  )\n")
    dsn.write_text(t[:j] + block + t[j:])

    # **入ったことを確かめる。**「書いたから効いている」と思わないこと。
    # structure の外に落ちていても Freerouting は黙って捨てるので、
    # **括弧を数え直して本当に structure の内側かを見る。**
    t2 = dsn.read_text()
    if "(layer_rule B.Cu" not in t2:
        raise SystemExit("layer_rule が入っていない")
    s = t2.index("(structure")
    k = t2.index("(autoroute_settings")
    depth = 0
    for j2 in range(s, len(t2)):
        if t2[j2] == "(":
            depth += 1
        elif t2[j2] == ")":
            depth -= 1
            if depth == 0:
                break
    if not s < k < j2:
        raise SystemExit(
            "autoroute_settings が structure の外にある（parser の中に"
            "落ちていないか）。この状態では黙って無視され、効果が無い")

JAR = Path(os.environ.get(
    "FREEROUTING_JAR",
    Path.home() / ".local/share/freerouting/freerouting-2.3.0.jar"))


def _java():
    """java の実行ファイル。Homebrew の openjdk は PATH に無いことがある。

    **あることを確かめるだけでは足りない。**macOS には `/usr/bin/java` と
    いうスタブが必ず存在し、実行すると「Java をインストールせよ」と出して
    失敗する。存在検査だけだとこれを選び、配線が黙って失敗する（実際に
    そうなった。PATH に openjdk が無い環境で起きる）。
    **`-version` が通ることまで確かめる。**
    """
    tried = []
    for cand in (shutil.which("java"),
                 "/opt/homebrew/opt/openjdk/bin/java",
                 "/usr/local/opt/openjdk/bin/java"):
        if not cand or not Path(cand).exists():
            continue
        tried.append(cand)
        try:
            r = subprocess.run([cand, "-version"], capture_output=True, timeout=30)
        except (OSError, subprocess.TimeoutExpired):
            continue
        if r.returncode == 0:
            return cand
    raise SystemExit(
        "動く java が見つからない。brew install openjdk を実行すること。\n"
        f"  試したもの: {tried or 'なし'}\n"
        "  （/usr/bin/java は macOS のスタブで、存在しても動かない）")


def _check_jar():
    if not JAR.exists():
        raise SystemExit(
            f"Freerouting が見つからない: {JAR}\n"
            "入手:\n"
            "  mkdir -p ~/.local/share/freerouting\n"
            "  curl -L -o ~/.local/share/freerouting/freerouting-2.3.0.jar \\\n"
            "    https://github.com/freerouting/freerouting/releases/download/"
            "v2.3.0/freerouting-2.3.0.jar\n"
            "別の場所に置くなら FREEROUTING_JAR で指定する")


# **2 層になったので、GND 専用層の予約は無くなった**（2026-08-12・指摘 2）。
#
# 4 層のときは In1.Cu を `(type power)` と宣言し直して、自動配線器に
# 「ここに信号を通すな」と全面予約していた。2 層では信号層と GND ベタ層が
# 同じ 2 枚を兼ねるので、**両方を予約したら配線する場所が無くなる。**
#
# したがって GND ベタは最初から配線を避けた歯抜けになる。分断された島を
# 繋ぎ直すのは gnd_fanout.stitch のスティッチングビアの仕事で、
# 繋がったかどうかは test_pcb が「GND の島が 1 つか」で見る。


# gen_pcb.py が自分で引いてしまうネット。**DSN から丸ごと外す。**
#
#   GND      両面のベタと gnd_fanout のビアで配り終えている
#   SW\d+_D  スイッチ → ダイオード。裏面の L 字 2 本で届く
#             （gen_pcb.prewire_switch_diode）
#   ROW\d+   行のバス。裏面の一直線で引く（gen_pcb.prewire_row_bus）。
#             **ダイオードの K 側は行ごとに y が完全に一致していて、
#             ライン上にスルーホールが無い**ので経路に迷いが無い。
#             自動配線器に任せると表裏を 5〜7 回行き来していた
#             （2026-08-14・利用者の指摘）。
#             ⚠️ 全部は外せない。**J_DB へ戻る 1 本だけは残す**——
#             コネクタは行のラインから外れた y にあり、直線では届かない。
#   V3V3     子基板で自分で引く（gen_daughterboard._prewire_power）。
#             4 つのパッドがほぼ一直線なのに Freerouting が 8.37mm・
#             6 セグメントで蛇行し、GND のスタブと交差した（2026-08-14）。
#             ⚠️ **主基板の V3V3 も対象になる。**あちらは FFC から各所へ
#             配るだけで prewire していないが、DSN から消えると未配線に
#             なるので、**子基板だけ**に効かせる（下の PREWIRED_DB）。
PREWIRED = re.compile(r"GND|SW\d+_D")

# 子基板だけ、これも自分で引いてある。
#
# ⚠️ **レーンを通る ROW を入れるのが対**（2026-08-14・利用者「D3〜D5 を XIAO
# パッドの外側を通るようにできませんか」）。`gen_daughterboard._prewire_rows`
# が列の外の帯に 3 本引くので、**ここに足さないと DSN に「未配線」として
# 残り、Freerouting が同じネットをもう一度引いて自分自身と交差する。**
# 2026-08-14 に手配線をやめた原因がまさにこれで、当時 ROW は
# protect にならないまま引かれていた（交差 5 件のうち 3 件が自己交差）。
# ⚠️ **SPARE も入れる**（2026-08-14・利用者）。D1 は用途未定だが
# FFC 12 番まで**列の外の帯を自分で引いてある**ので、ROW と同じ扱い。
# ⚠️ **右列を自分で引いたら、その 5 本も入れる**（2026-08-14）。
# SPI_MOSI / SPI_SCK / CS / SPARE2。入れないと Freerouting が二重に引く。
PREWIRED_DB = re.compile(
    r"GND|SW\d+_D|V3V3|ROW_[A-E]|SPARE2?|SPI_MOSI|SPI_SCK|CS")


# Freerouting に上乗せして要求するクリアランス（µm）。
#
# **Freerouting は要求ぎりぎりを狙い、丸めで下回ることがある。**
# 実測（2026-08-13）: 0.200mm を要求したのに 0.187〜0.198mm で引き、
# KiCad の DRC がクリアランス違反にすることがある。
#
# KiCad 側の判定は 0.2mm のまま動かさない（そちらを緩めたら意味が無い）。
# **自動配線器にだけ多めに言う。**
#
# 値は左右**共通**（利用者の要望。基板ごとに違う値を使う非対称は避ける）。
# マージンを上げすぎると、配線が入れる隙間そのものが狭くなり未配線が
# 増えるトレードオフがある（40µm で右の未配線が 2→3 に悪化した）。
#
# **2026-08-14 に 15 → 20 へ上げた。**この日の変更（電源鎖の移動・
# 行バスの直線化・VBATT_RAW 廃止・V3V3 の 0.3→0.2mm）のあと、
# 15 では丸め不足が顕在化して DRC のクリアランス違反が出た
# （左 1 件・右 3 件。実測 0.1917〜0.1919mm ＜ 規則 0.2000mm）。
#
#     15µm … 違反 左1/右3、未配線 左0/右1
#     20µm … **違反 0/0/0、未配線 左2/右0**  ← いまここ
#     25µm … 違反 0/0/0、未配線 左2/右1
#
# 左に残る 2 本は ROW3/ROW4 が J_DB へ降りる枝（マージンとは別の話。
# J_DB の ROW パッドの並びが行バスの y 順と食い違っていて交差する）。
DSN_CLEARANCE_MARGIN_UM = 30


def _ask_freerouting_for_a_little_more_clearance(dsn):
    """DSN のクリアランスだけ少し増やす。KiCad の設計規則は変えない。

    `(clearance N)` の N は µm（DSN の冒頭が `(unit um)`）。
    **`(type smd_smd)` の行は触らない**——あれは同じ部品の中の
    パッドどうしの許容で、増やすとファンアウトが通らなくなる。
    """
    t = dsn.read_text()
    n = [0]

    def bump(m):
        n[0] += 1
        return f"(clearance {int(m.group(1)) + DSN_CLEARANCE_MARGIN_UM})"

    t = re.sub(r"\(clearance (\d+)\)(?!\s*\(type)", bump, t)
    if not n[0]:
        raise SystemExit(
            "DSN にクリアランスの指定が見つからない。KiCad の書式が"
            "変わった可能性がある。**黙って進めない**"
            "（Freerouting が丸めで規則を下回る）")
    dsn.write_text(t)


def _strip_prewired(dsn, pattern=PREWIRED):
    """自分で引いたネットを DSN から完全に消す。

    残すと Freerouting が「未配線だ」と思って引き直し、二重になる。

    **「ピンだけ消してネットは残す」ような中途半端なやり方はしない。**
    Freerouting が NullPointerException で落ちる（実測。ヘッドレスの
    つもりでも GUI が立ち上がって例外ダイアログが出る）。ネット定義・
    クラスの一覧・plane 宣言をまとめて消すこと。

    配線材は `(type protect)` に変える。ネットを持たない固定の障害物
    として渡すと Freerouting はそこを避けて配線する。
    **消してしまうと避けてくれず、上から配線されて短絡する。**
    """
    t = dsn.read_text()
    names = sorted({n for n in re.findall(r"\(net (\S+)", t) if pattern.fullmatch(n)})
    for n in names:
        e = re.escape(n)
        t = re.sub(rf"\s*\(plane {e} \(polygon [\s\S]*?\)\)", "", t)
        t = re.sub(rf"\s*\(net {e}\s*\n\s*\(pins [^)]*\)\s*\n\s*\)", "", t)
        t = re.sub(rf"(\(class \S+ [^)]*?)\b{e}\b", r"\1", t)
        t = t.replace(f"(net {n})(type route)", "(type protect)")
    # **消さずに残すが、動かしてほしくないネット**（2026-08-17・
    # 利用者「このキーマトリクスの配線を凍結させてください」）。
    #
    # ROW と COL は**ネットごと消せない**——最後の 1 本（ROW は J_DB、
    # COL は U1）は Freerouting に引かせる必要があるため。しかし
    # `(type route)` のままだと**引いた線ごと作り直される**。
    #
    # ⚠️ **注記は「protect で渡してある」と書いていたが、実際には
    # なっていなかった**（2026-08-17 に実測。ROW も COL も route）。
    # 上の置換は「消したネット」にしか掛からないので、消さない
    # ROW/COL には効いていなかった。**ここで明示的に protect にする。**
    # ⚠️ **protect にしない**（2026-08-18・実測）。
    #
    # 2026-08-17 にここで ROW/COL を protect にしたが、**protect は
    # 「動かすな」ではなく「触るな」**なので、Freerouting は**その線に
    # 繋ぎ込むこともできなくなる。**結果、COL→U1 が 6 本・ROW→J_DB が
    # 5 本、まるごと未配線として残った（左 11 件・右 15 件）。
    # 「最後の 1 本だけは Freerouting に引かせる」という目的と、
    # protect という手段が矛盾していた。
    #
    # **凍結は `replay_matrix` が担保する**——SES 取り込みのあとに
    # 未配線の板から写し直すので、Freerouting が途中でどう動かしても
    # 最終的な形は gen_pcb が引いたものになる。

    left = [n for n in re.findall(r"\(net (\S+)", t) if pattern.fullmatch(n)]
    if left:
        raise SystemExit(
            f"{dsn.name}: 消しきれていないネットがある: {sorted(set(left))}\n"
            "DSN の書式が変わった可能性がある。残すと Freerouting が"
            "二重配線するか NPE で落ちる")
    dsn.write_text(t)


# **書き出し先。**既定は本番の pcb/。
#
# ⚠️ **試しの配線を本番に書かないこと**（2026-08-18・利用者「本番
# ファイルではなく別フォルダを作るべき」）。私は「違反があってもいいので
# 配線して」を本番を回すことだと解釈し、**U1/U2 が決まるまで本番は
# 触らないという合意を破って 3 枚を上書きした。**
#
#     "$KPY" tools/autoroute.py right --out pcb/try
OUT_DIR = None          # None なら PCB（本番）


def _out_dir():
    return OUT_DIR or PCB


def _route_once(half, seed):
    """未配線の基板を 1 回配線して、その結果を返す。"""
    _check_jar()
    src = UNROUTED / f"hhkb_split_{half}.kicad_pcb"
    if not src.exists():
        raise SystemExit(
            f"未配線の基板が無い: {src}\n"
            'KiCad の Python で "tools/gen_pcb.py --no-route" を実行すること')

    # **DSN の元も正本にする**（2026-08-22）。
    #
    # ⚠️ **`pcb/unrouted/` から DSN を作ると、利用者が引いたレーンが
    # 入らない。**Freerouting はそこを空いていると思って線を引き、
    # 実測で **短絡 7 件**（COL8 のレーンの上に COL2/COL5/COL6 が乗った）。
    # レーンは「既にある配線」として渡す必要がある。
    golden0 = ROOT / "pcb" / "matrix_only" / f"hhkb_split_{half}.kicad_pcb"
    board = pcbnew.LoadBoard(str(golden0 if golden0.exists() else src))
    dsn = PCB / f"_{half}.dsn"
    ses = PCB / f"_{half}.ses"
    if not pcbnew.ExportSpecctraDSN(board, str(dsn)):
        raise SystemExit(f"{half}: DSN の書き出しに失敗した")
    _strip_prewired(dsn, PREWIRED_DB if half not in HALVES else PREWIRED)
    _ask_freerouting_for_a_little_more_clearance(dsn)
    # ⚠️ **子基板には入れない**（2026-08-15・利用者「明らかに配線できそう
    # ですけどね」）。**`(autoroute_settings)` があるだけで、Freerouting
    # 2.3.0 が子基板のネットを 1 本も見なくなる。**
    #
    # 実測（同じ DSN で、ブロックの有無だけを変えた）:
    #
    #   ブロックあり … ログ "started with **0** unrouted nets" / SES 18 行（空）
    #   ブロックなし … ログ "started with **4** unrouted nets" / SES 98 行
    #
    # **中身は関係ない。**`(fanout on)`・`(start_ripup_costs)` だけ・
    # `layer_rule` だけ、と 4 通り試して**すべて 0**。ブロックの存在が効く。
    # ネットが 2 本しか残らない（他は PREWIRED_DB で消える）ことが
    # 引き金だと思われるが、Freerouting 側は何も警告を出さない。
    #
    # **これが未配線 4 件の正体だった。**VBATT_SW / VBATT_SENSE の 4 接続は
    # 直線経路に障害物が無く（実測 2.2〜4.0mm・邪魔なし）、
    # 「密集して引けない」のではなく**そもそも渡っていなかった**。
    #
    # 主基板では正常に働く（左: started_with=60 で両方とも配線される）ので
    # そちらは残す。ただし**層コストの効果は測ると逆**だった——
    # 左の F.Cu 比率は **あり 23.3% / なし 19.8%**。3dd43b8 の
    # 「F.Cu 22-25% → 10-12%」はこのブロック以外の要因で説明する必要がある。
    # **主基板でも外すべきかは別途（open-gaps 行き）。**
    if half in HALVES:
        _autoroute_settings(dsn)

    # Freerouting のログは終わりに「N violations」と出すが、これは
    # protect にしたファンアウトどうしの接触を数えているだけ。
    # **本当の判定は KiCad の DRC**（tools/drc.py）。ここの数字で
    # 良否を決めないこと。
    subprocess.run(
        [_java(), "-jar", str(JAR), "-de", str(dsn), "-do", str(ses),
         "-mp", str(PASSES), "--gui.enabled=false"],
        check=True)
    if not ses.exists():
        raise SystemExit(f"{half}: Freerouting が SES を出さなかった")

    if not pcbnew.ImportSpecctraSES(board, str(ses)):
        raise SystemExit(f"{half}: SES の取り込みに失敗した")

    # **トラック幅を揃える。**
    #
    # Freerouting は同じ入力でも**たまに 0.12mm / 0.15mm の線を引く**
    # （2026-08-12 に左で 4 本出た。前回の配線では 1 本も無かった）。
    # 0.12mm は JLCPCB の最小 0.127mm を割るので DRC が赤になる。
    # **配線し直すたびに当たるかどうかが変わる**ので、ここで潰す。
    # 太くする向きなので、クリアランスは DRC で確認する。
    # **ネットごとに、そのクラスの幅まで引き上げる。**
    # 以前は既定幅（0.2mm）を下回るものだけ直していたが、
    # 電源をクラス分けしたので、V3V3 が 0.225mm で出てくることがある
    # （クラスは 0.3mm）。**細い方向のばらつきは全部ここで潰す。**
    from pcb_rules import TRACK_W
    _w = pcbnew.FromMM(TRACK_W)
    _fixed = 0
    for t in board.GetTracks():
        if t.GetClass() == "PCB_TRACK" and t.GetWidth() < _w:
            t.SetWidth(_w)
            _fixed += 1
    if _fixed:
        print(f"   {half}: 細いトラック {_fixed} 本を {TRACK_W}mm へ揃えた")

    # **電源をクラスの幅まで引き上げることはしない。**
    #
    # 一度やったら DRC のクリアランス違反が増えた（左 0→1・右 1→2）。
    # 調べると、Freerouting は**狭いところで自分から幅を絞っている**。
    # つまり利用者が求めた「太くできるところは太く、できないところは
    # しない」を、自動配線器が既にやっている。**後から一律に太らせるのは、
    # その正しい判断を壊す行為だった。**
    # 幅の分布は test_pcb が見る（大半がクラスの幅であること）。

    # **自分で引いた配線を立て直す。**
    #
    # ImportSpecctraSES は既存の配線を全部作り直すので、配置段階で
    # 引いたものが消える（実測: GND のビア 7 個 → 0 個）。どちらも
    # DSN から外してあり SES にも入っていないので、ここで復活させないと
    # 繋がらないまま残る。
    #
    # 位置はどちらも決定的に決まるので配線前と同じところに戻り、
    # Freerouting はそこを避けて配線済みなので衝突しない。
    # **マトリクスがある基板だけ。**子基板にはスイッチも行も無い。
    if half in HALVES:
        # **マトリクスは未配線の板から「写す」。引き直さない。**
        # （2026-08-17・利用者「このキーマトリクスの配線を凍結させて」）
        #
        # ⚠️ **引き直すと同じ答えにならない。**経路は板の上の物から
        # 決まるが、SES 取り込み後はビアが 38 → 1217 個に増えている。
        # 実測で 13 ホップが「障害物」で落ちた。**凍結とは同じ手順を
        # 回すことではなく、同じ結果を置き直すこと。**
        # **正本は `pcb/matrix_only/`**（2026-08-22・利用者の指示 A）。
        #
        # ここには利用者が KiCad で引いた分が入っている——列を MCU へ
        # 戻す表面のレーン 7 本、COL0→U1、V3V3、COL8 のバス。
        # **規則として書き下すのではなく、現物を正本にする。**
        # 私が規則を書こうとして 3 回失敗している（着地で U1 の他の
        # パッドを横切る／レーンを縦に伸ばして他のレーンと交差する／
        # 跨がない行に橋を架ける）。
        #
        # 無ければ `pcb/unrouted/`（gen_pcb が引いた分だけ）に落ちる。
        golden = ROOT / "pcb" / "matrix_only" / f"hhkb_split_{half}.kicad_pcb"
        ref = golden if golden.exists() else src
        n_mx, n_mv = replay_matrix(board, pcbnew.LoadBoard(str(ref)))
        print(f"   {half}: マトリクスを写した {n_mx} 区間 / ビア {n_mv} 個"
              f"（正本 {ref.parent.name}/）")
    else:
        # **電源も引き直す。**上の行バスと同じ理由——**SES 取り込みは
        # 既存の配線を全部置き換える**ので、gen_daughterboard で引いた
        # V3V3 と GND の引き出しは消えている（実測: unrouted に V3V3 6・
        # GND 7 本あったものが、取り込み後は V3V3 0・GND 4 になっていた。
        # 2026-08-14）。DSN では protect の障害物として渡してあるので、
        # Freerouting はここを避けて残りを引いている。
        from gen_daughterboard import _prewire_power, _prewire_rows
        _prewire_power(board)
        # **列の外のレーン 3 本も立て直す**（2026-08-14）。
        # 上と同じ理由——SES 取り込みが既存の配線を全部作り直すので、
        # gen_daughterboard で引いた 12 区間が消える（実測: 立て直しを
        # 入れる前は 3 本とも「Missing connection」になった）。
        _prewire_rows(board)
        # **右列も同じ**（2026-08-14）。SES 取り込みで消えるので立て直す。
        from gen_daughterboard import RIGHT_OUTER_LANE_PADS
        _prewire_rows(board, RIGHT_OUTER_LANE_PADS, side=+1)
        # **子基板は配線後にベタを敷く**（2026-08-14・open-gaps #41）。
        # 主基板は gen_pcb が配置段階で敷いてから配線するが、子基板は
        # 手配線をやめて Freerouting に移したので、主基板と同じ
        # 「配線 → ベタ → ビア」の順に揃える。
        _restore_rule_area_layers(board)
        _pour_daughterboard_ground(board)
    n_fan = gnd_fanout.place(board)

    # **順序が効く。狙って打つものを先に、埋め草を後に。**
    #
    # 最初は格子（stitch）を先に打っていたが、**配線の脇という一番
    # 効く場所が格子に先取りされ、フェンスが並ばなかった**
    # （2026-08-13。利用者が絵を見て「斜め線のところにビアが無い」と
    # 気づいた）。長い配線の脇は戻り電流の横断口なので、そちらが先。
    #
    # どちらも配線が終わってから打つ。配線を障害物として避けたいので、
    # 配線前に打つと置き場所を見誤る。
    n_fe, n_long = gnd_fanout.fence(board)
    # **禁止域のふちは格子より先に縫う**（2026-08-16）。格子は 6.5mm
    # ピッチなので、禁止域の脇の幅 1mm の帯には格子点が落ちない。
    # 先に打っておけば、格子はこれを障害物として避ける。
    n_ring = gnd_fanout.ring(board)
    n_st, n_skip = gnd_fanout.stitch(board)
    print(f"   {half}: GND ビア ファンアウト {n_fan} 個 / "
          f"長い経路 {n_long} 本の脇に {n_fe} 個 / "
          f"禁止域のふちに {n_ring} 個 / "
          f"格子で埋めた {n_st} 個（置けなかった格子点 {n_skip}）")

    # **配線後に 1 本ずつ太らせる後処理は入れていない**（2026-08-12）。
    #
    # 指摘 8 は gen_pcb.POWER_CLASSES のクラス分けで達成している
    # （V3V3 = 0.3mm＝FFC の 0.30mm パッドに載る上限、他 = 0.6mm）。
    # そのうえで「開けたところだけさらに太く」する後処理も書いたが、
    # **自前の当たり判定が取りこぼし、DRC のクリアランス違反を
    # 3 回続けて出した。**得られるのは V3V3 が 15mA しか流さない区間で
    # 太くなることだけなので、割に合わないと判断して外した。
    # 実装も消した（使わないものを残さない）。

    # **離島になった GND を、ビアで本土へ繋ぎ戻す**（指摘 4・5）。
    #
    # 2 層では配線がベタを割るので、GND のどこにも触れない区画ができる。
    # そういう銅は電位が決まっておらず GND ではない。**消すのではなく
    # 繋ぐ**——反対面のベタを経由すれば戻せる。
    #
    # この中でゾーンの塗り直しまで済ませる（ビアを打つとベタの形が
    # 変わるので、繰り返して収束させる必要がある）。
    n_is, left = gnd_fanout.stitch_islands(board)
    print(f"   {half}: 離島に打ったビア {n_is} 個 / 繋げ切れなかった区画 {left}")

    out = _out_dir() / f"hhkb_split_{half}.kicad_pcb"
    board.Save(str(out))
    dsn.unlink()
    ses.unlink()

    # **どの未配線基板から作られたかを残す。**
    # これが無いと「配置を変えたのに配線し直していない」が検出できない。
    #
    # バイト列ではなく指紋を使う。KiCad は保存のたびに UUID と
    # フットプリントの並び順を変えるので、バイトのハッシュは
    # 「再生成しただけ」でも変わってしまう（boardhash.py の説明を見る）。
    board.BuildConnectivity()
    left_over = board.GetConnectivity().GetUnconnectedCount(False)
    rec = {
        "board": out.name,
        "unrouted": src.name,
        "unrouted_fingerprint": boardhash.fingerprint(src),
        "freerouting": JAR.name,
        "passes": PASSES,
        "attempt": seed,
        "unconnected": left_over,
    }
    (_out_dir() / f"route_{half}.json").write_text(
        json.dumps(rec, ensure_ascii=False, indent=2) + "\n")
    return rec


# **引き直しても無駄。Freerouting は決定的。**
#
# 「実行のたびに結果が揺れるので、0 が出るまで引き直す」という仕組みを
# 書きかけたが、**仮定を検証したら間違いだった**（2026-08-13）。
# 同じ入力で 3 回引いて未配線は 3 回とも同じ本数。揺れて見えていたのは
# こちらがコードを変えていたからで、Freerouting のせいではない。
#
# パス数を増やしても解けない（100 → 300 → 800 で未配線は減らなかった）。
# **残るのは配置の問題**なので、そちらで解く。


def run(half):
    """未配線の基板を配線し、記録を残して返す。"""
    return _route_once(half, 1)


def main():
    # **子基板も同じ仕組みで配線する**（2026-08-14・open-gaps #41）。
    # 手書きのルータをやめたので、3 枚とも Freerouting を通る。
    #
    # **直した基板だけを指定できる**（2026-08-14・利用者「DB だけの修正に
    # 左右も再配線する意味ある？」）。無い。Freerouting は毎回わずかに
    # 違う経路を出すので、**触っていない基板まで sha256 が変わり**、
    # drc_*.json の差分が汚れて「何を直したか」が読めなくなる。
    #
    #     "$KPY" tools/autoroute.py daughterboard
    global OUT_DIR
    args = sys.argv[1:]
    if "--out" in args:
        i = args.index("--out")
        OUT_DIR = ROOT / args[i + 1]
        OUT_DIR.mkdir(parents=True, exist_ok=True)
        del args[i:i + 2]
        print(f"書き出し先: {OUT_DIR}（本番の pcb/ は触らない）")
    targets = args or list(BOARDS)
    unknown = [t for t in targets if t not in BOARDS]
    if unknown:
        raise SystemExit(f"知らない基板: {unknown}／選べるもの: {list(BOARDS)}")
    for half in targets:
        rec = run(half)
        print(f"OK {half:5s} {rec['unrouted']} → {rec['board']}"
              f"  ({rec['freerouting']}, {rec['passes']} パス)")
    print("\n配線した。次: .venv/bin/python3 tools/drc.py")
    return 0


def _pour_daughterboard_ground(board):
    """**子基板の GND ベタを両面に敷く**（2026-08-14・open-gaps #41）。

    2026-08-14 まで裏面だけだった。主基板は最初から両面
    （`gen_pcb.GND_POUR_LAYERS`）なのに、**2.4GHz のアンテナが載って
    いるこの基板だけ片面**という非対称だった（利用者の指摘
    「MAIN PCB に施していて DB に施していないものがある」）。
    基準電位の安定はここでこそ効く。

    アンテナの真下は `gen_daughterboard._antenna_keepout` が両面とも
    抜いてある（禁止域は配置の段階で入っていて、DSN にも乗る）。
    """
    from gen_daughterboard import DB_D, DB_W
    from gen_pcb import ORIGIN
    gnd = board.FindNet("GND")
    if gnd is None:
        raise SystemExit("子基板に GND が無い")
    for layer in (pcbnew.F_Cu, pcbnew.B_Cu):
        zone = pcbnew.ZONE(board)
        zone.SetNet(gnd)
        zone.SetLayer(layer)
        zone.SetLocalClearance(pcbnew.FromMM(0.25))
        # **サーマルリリーフを使わずベタ付けにする。**GND は放熱より
        # 接続の確実さと低インピーダンスを優先する。リリーフのままだと
        # FFC の GND パッドでスポークが 1 本しか取れず、DRC が
        # 「接続が不完全」と出た。
        zone.SetPadConnection(pcbnew.ZONE_CONNECTION_FULL)
        zone.SetIslandRemovalMode(pcbnew.ISLAND_REMOVAL_MODE_ALWAYS)
        pts = pcbnew.VECTOR_VECTOR2I()
        for dx, dy in ((-1, -1), (1, -1), (1, 1), (-1, 1)):
            pts.append(pcbnew.VECTOR2I_MM(ORIGIN[0] + dx * DB_W / 2,
                                          ORIGIN[1] + dy * DB_D / 2))
        zone.AddPolygon(pts)
        board.Add(zone)
    pcbnew.ZONE_FILLER(board).Fill(board.Zones())


def _restore_rule_area_layers(board):
    """**SES 取り込みで消えたルール領域の層を戻す**（2026-08-14・#41）。

    アンテナの禁止域は `gen_daughterboard` が F.Cu と B.Cu を指定して
    作るが、**DSN → Freerouting → SES を往復すると層が空になる**
    （`GetLayer()` が -1 になる。実測）。層を持たないゾーンは何も禁止
    しないので、**そのあとに敷いたベタがアンテナの真下に入り込む**
    （実測 3297 頂点。test_daughterboard が気づいた）。

    ⚠️ **「宣言したから効いている」と思わないこと。**この案件で
    3 回目の同じ型（#23 の禁止域・主基板の的外れな禁止域・これ）。
    """
    n = 0
    for zone in board.Zones():
        if not zone.GetIsRuleArea():
            continue
        ls = pcbnew.LSET()
        for lay in (pcbnew.F_Cu, pcbnew.B_Cu):
            ls.addLayer(lay)
        zone.SetLayerSet(ls)
        n += 1
    if n:
        print(f"   ルール領域 {n} 個の層を戻した（SES 往復で消える）")


if __name__ == "__main__":
    sys.exit(main())
